shemtov/Bg_Bed/panel_shemi/src/main.cpp

// ============================================================
// PANEL SHEMI - TEST 074 - MATCHED PAIR + SEIKO NIGHT SCREENSAVER
// ============================================================
//
// Board: Waveshare ESP32-S3-Touch-LCD-7B, 1024 x 600
// TEST074 - BUILD FIX FOR AM / PM BUTTONS
//   TEST073 did not compile because seedFromRTC() calls
//   refreshAmPmButtons() before the compiler has seen its declaration.
//   Adds the forward declaration before seedFromRTC().
//   No UI behavior, RTC, RS485, massage or audio logic changed.
//   NOT YET RUN ON HARDWARE.
// TEST073 - CLOCK SETTING: DIRECT AM / PM BUTTONS
//   Removes the 12-hour ON/OFF switch from the Clock settings tab.
//   Replaces it with two small round buttons: AM and PM.
//   The selected half-day lights green; the other stays dark.
//   Pressing AM/PM changes only the half-day, not the displayed hour.
//   Hour +/- now cycles 1..12 inside the selected AM/PM half.
//   The DS3231 still stores and receives 24-hour time internally.
//   Clock display is now always 12-hour AM/PM.
//   Massage, feedback, RTC validity and RS485 logic are unchanged.
//   NOT YET RUN ON HARDWARE.
// TEST072 - BUILD FIX FOR MASSAGE SLIDER VALUE FONT
//   TEST071 did not compile because lv_font_montserrat_20 is not enabled
//   in this Waveshare LVGL build.
//   The live percentage labels above the four massage sliders now use
//   the already-enabled lv_font_montserrat_26.
//   No massage mapping, slider geometry, feedback, RTC or RS485 logic changed.
//   NOT YET RUN ON HARDWARE.
// TEST071 - MASSAGE FULL + SLIDER READOUT
//   Fixes the FULL tile mapping. FULL is UI tile index 3, not 11.
//   Tile 3 now sends CMD_ALL=100 to the BedBox.
//   UI tiles after FULL map down by one to BedBox presets 3..10.
//   FULL label changed from "מלא" to "הכל".
//   Four zone sliders are slimmer, while the knob stays visually large.
//   Each slider now shows its exact live percentage above it.
//   The displayed number follows both finger movement and BedBox feedback.
//   RTC TEST070 diagnostic remains unchanged.
//   NOT YET RUN ON HARDWARE.
// TEST070 - RTC DIAGNOSTIC MADE VISIBLE
//   TEST069 printed the RTC dump too early in boot, before the Serial
//   Monitor was reliably attached, so the useful line could be missed.
//   While CLOCK NOT READY persists, TEST070 prints the full RTC dump
//   every 5 seconds. No RTC state is changed and no Set Time is done.
//   Massage, feedback and RS485 behaviour are unchanged.
//   NOT YET RUN ON HARDWARE.
// TEST069 - RTC BACKUP / OSF DIAGNOSTIC
//   Diagnostic-only change.
//   Prints raw DS3231 time/date and status register 0x0F at boot.
//   This tells us whether the clock value survived power-off and
//   whether OSF (Oscillator Stop Flag, bit 7) is set.
//   Massage, feedback and RS485 behaviour are unchanged.
//   NOT YET RUN ON HARDWARE.
// TEST068 - MASSAGE CLOSED LOOP RESTORED
//   TEST067 restored BedBox -> panel feedback, but the current 7-inch
//   massage handlers only changed the UI and printed to USB Serial.
//   They did NOT send motor commands to the BedBox.
//   TEST068 restores the proven 4-byte BedBox downlink:
//       {bedId, cmd, target, value}
//   on the SAME onboard RS485 Serial1 bus.
//   Commands:
//       0 OFF, 1 ALL, 2 ZONE, 4 PRESET, 5 TIMER
//   The 12th "Full" tile sends ALL=100; patterns 0..10 send PRESET.
//   TEST067 feedback remains in place:
//       {bedId, 20, zone, level}
//   NOT YET RUN ON HARDWARE.
// TEST067 - BEDBOX FEEDBACK RESTORED
//   Restores the hardware-proven TEST077/BedBox TEST012 feedback behaviour
//   to the current 7-inch panel.
//   BedBox reports remain the proven 4-byte form:
//       {bedId, 20, zone, level}
//   The panel now accepts those reports on the SAME RS485 stream while
//   preserving the existing 14-byte A5 TIME/ACK traffic.
//   Slider updates are display-only: lv_slider_set_value() does not
//   generate another motor command.
//   NOT YET RUN ON HARDWARE - build/flash required for confirmation.
//
// WHAT CHANGED IN TEST 083:
//   Fixes TEST082 build failure: the generated setup Serial.println()
//   line lost its closing quote/parenthesis during text replacement.
//   TEST083 uses safe whole-line replacements and preserves valid C++.
//   Ira still uses the full 7-inch UI and receives clock/date from
//   Shemi over onboard RS485 (RX GPIO15, TX GPIO16, 115200 8N1).
//
// NOT YET COMPILED OR RUN ON HARDWARE.
//
//
// WHAT CHANGED vs TEST 055
//   THE LONG PRESS NEVER FIRED, and the approach was the fault. I
//   leaned on LV_EVENT_LONG_PRESSED, which only fires if the input
//   driver's long_press_time is what I set it to - a field inside
//   Waveshare's port that I set blind at boot and cannot verify
//   from here. Depending on it was the mistake.
//
//   THE PANEL TIMES THE HOLD ITSELF NOW. millis() on press, millis()
//   on release, subtract. Under 2 seconds flips the power; 2 seconds
//   or more opens the detail screen. No LVGL setting involved, so
//   there is nothing left to be silently wrong.
//
//   IT ACTS ON RELEASE, not at the 2 second mark. A press that
//   triggers while your finger is still down needs a timer running
//   against every tile; measuring on release is exact, needs
//   nothing running, and cannot fire twice.
//
//   AND IT PRINTS THE MEASURED HOLD - "[tile] AC held 2340 ms" - so
//   if 2 seconds turns out to be the wrong threshold for you, we
//   will be reading real numbers instead of guessing again.
//
//   PRESS_LOST is handled too: slide off the tile and nothing
//   happens, which is the standard way out of a press you did not
//   mean.
//
// WHAT CHANGED IN TEST 054 vs TEST 053
//   Alarm screen:
//     - "Hour" and "Minute" titles above their plus/minus groups,
//       the same treatment the Clock tab got in TEST 050
//     - the whole setter is CENTRED, horizontally and vertically -
//       it sat 110 px from the top before, which put it in the
//       upper third rather than the middle
//
//   THE FLEX ROW IS GONE, and it had to be: a flex row lays its
//   children out in a line and cannot put a heading over one of its
//   own columns. Absolute positions instead, exactly as the Clock
//   tab needed for the same reason.
//
//   Centred means centred on the SCREEN, so the numbers sit level
//   with the middle of the glass, not with the space left over
//   under the switches.
//
// WHAT CHANGED IN TEST 052 vs TEST 051
//   HANDS: thinner, SQUARE ended, and hollow to the tip.
//     - lv_line rounded caps turned OFF, so the ends are flat
//       rectangles instead of domes
//     - hour 20 px outer over a 12 px dark core, minute 12 over 6.
//       Was 30 over 12 and 20 over 8 - that is what made them heavy
//     - THE TRIANGLE TIPS ARE GONE. They were the weight and the
//       roundness both, and a hollow rectangle cannot end in a
//       solid point without stopping being hollow. The core now
//       runs almost to the end, so the tip reads open.
//
//   SECOND HAND IS RED, keeping the green lume dot.
//
//   NINE GETS ITS MARKER BACK - a lying pill, matching three.
//
//   THE DATE WINDOW MOVED to the right, midway between the centre
//   and the three o'clock pill, which is where the freed space is
//   now that nine is a marker again.
//
//   TEMPERATURE RIGHT, HUMIDITY LEFT was already done in TEST 050 -
//   which never ran, because it did not compile. Nothing to change;
//   it arrives with this build.
//
// WHAT CHANGED IN TEST 051 vs TEST 050
//   TEST 050 would not compile: refreshStations() was placed with
//   the radio widget pointers, above kStation and radioStation
//   which it reads. It sits just before refreshRadio now, after
//   both. Third member of the use-before-declaration family
//   tonight - so the delivery audit no longer takes a hand-made
//   list of names, it derives every file-scope variable and
//   function from the file itself and checks all of them.
//
// WHAT CHANGED IN TEST 050 vs TEST 049
//   Five prompts of remarks, all in one test.
//
//   EVERYWHERE
//     - back button is a SQUARE, 56 by 56, teal. "Square" was said
//       twice and clearly; the later garbled sentence asked for a
//       nicer colour, so amber went and teal came.
//     - the flip switch: the knob travels to the ENDS of a wider
//       pill, and when OFF the word disappears - knob position
//       says it alone. ON still says ON.
//
//   RADIO
//     - now-playing name at the top: gone
//     - title is Hebrew, drawn with font_hebrew_28
//     - station buttons are DULL until chosen; the chosen one gets
//       its full colour plus a white frame - much stronger than
//       the rest, as asked
//     - the audionode note under the stations: gone
//     - MAX at the right end of the volume slider
//
//   MASSAGE
//     - the pattern-name status at the top right (the "something I
//       do not know what sign it is"): gone. It was lblMassMode.
//     - the Massage caption beside the switch: gone
//     - the lying figure dropped well below the sliders
//
//   SETTINGS, CLOCK
//     - a title above every plus/minus group - Hour, Minute, Day,
//       Month, Year - bigger and brighter than the old grey
//     - the 12 hour switch moved to the bottom, caption under it
//
//   SETTINGS, DISPLAY
//     - "Response speed" now says what it is for: the reaction of
//       the AUTO BRIGHTNESS
//     - the switch caption sits UNDER the switch, bigger
//
//   SCREENSAVER
//     - hands rebuilt as SKELETON hands: two long bright rails with
//       a dark gap between them - an outer line with a face-dark
//       line over its middle - and a FILLED triangle tip, wider
//       than before
//     - the twelve pip is filled solid
//     - three and six are pills now, like nine was - three lying,
//       six standing, both pointing at the centre
//     - the date window moved to the LEFT, taking nine's place
//     - temperature RIGHT, humidity LEFT - swapped as asked - and
//       both drawn a step larger through transform zoom, because 48
//       is the largest font this build carries
//
// WHAT CHANGED IN TEST 049 vs TEST 048
//   TEST 048 would not compile. The new tile handlers - evACShort,
//   evFanShort - sit early in the file with the other tile code,
//   but fanSpeed, acTemp, refreshFan and refreshAC are all defined
//   hundreds of lines below them. The same use-before-declaration
//   mistake as TEST 032, caught by the compiler instead of the
//   audit because the audit only watched variables, not functions.
//
//   fanSpeed and acTemp moved up beside fanOn and acPower, where
//   they should have lived all along. refreshFan and refreshAC are
//   forward declared with the other forwards. The audit now checks
//   function calls too.
//
// WHAT CHANGED IN TEST 048 vs TEST 047
//   One line. Where the Seiko carries its red text below the
//   centre - MAGNETIC RESISTANT on the photograph - this dial says
//
//       Ira & Shemi Bengiat
//
//   in the same red, same place, small like on the watch. Spelled
//   the way Shemi spelled it. If it should be Hebrew instead, that
//   is a pre-reversed string away - say so.
//
// WHAT CHANGED IN TEST 047 vs TEST 046
//   The watch face redone against the photograph Shemi sent - a
//   Seiko Prospex Tuna. What was taken from it:
//
//   HANDS. The hour hand is BROAD - a wide shaft with a pointed
//   tip. The minute hand is longer and slimmer, same pointed tip.
//   The second hand is a thin line with a LUME DOT near the tip and
//   a counterweight tail past the centre - that dot is the most
//   recognisable thing on the watch and it moves with the hand,
//   realigned every second.
//
//   A DATE WINDOW AT THREE, where the Tuna has its date: a small
//   framed rectangle showing the day of the month, updated when the
//   day changes. The dot at three gave its place to it.
//
//   A HORIZONTAL PILL AT NINE, as on the photograph, instead of a
//   round dot.
//
//   The pips at twelve and six stay as Shemi specified them - the
//   six o'clock pip is his instruction and it stands even though
//   the Tuna itself carries a dot there.
//
//   Dots remain at 1, 2, 4, 5, 7, 8, 10, 11.
//
// WHAT CHANGED IN TEST 046 vs TEST 045
//   TWO FACTS BEFORE THE FEATURES, checked in the repo rather than
//   assumed:
//     - The AC detail screen here was a stub. The old panel's full
//       one - modes, fan speeds, swing, the honest "shows what was
//       last commanded" note - is now ported: Cool/Heat/Dry/Fan/
//       Auto, Low/Med/High/Auto, Swing on/off, temp 16-30, room
//       reading beside the target.
//     - There is NO fan screen in the old panel to copy. buildFan
//       does not exist in that file; the fan screen here was
//       written fresh for this board in TEST 017. It stays as it
//       is. If TEST 082 had one, it never reached the repo.
//
//   SHORT PRESS AND LONG PRESS ON THE HOME TILES, for fan and AC:
//     - a short press flips the power and stays on the home screen
//     - holding for 2 seconds opens the detail screen
//   The touch driver's long press threshold is set to 2000 ms at
//   boot - the LVGL default is 400, which is a twitch, not a hold.
//   Massage and radio tiles keep their single press - Shemi asked
//   for the two devices you mostly just switch on and off.
//
//   The AC power on the tile and the one on the screen go through
//   ONE function, so the two can never disagree about what "on"
//   means.
//
// WHAT CHANGED IN TEST 045 vs TEST 044
//   Watch face again, per Shemi:
//     - the dots doubled: 40 px core, about 6 mm, glow scaled with
//       them
//     - the arrowheads cut down - they were slabs; a dive watch
//       hand is mostly shaft with a modest tip
//     - a second pip at SIX, mirrored: flat edge at the bottom,
//       apex pointing up at the centre. The dot at six gave its
//       place to it, the same way twelve's did.
//     - temperature TOP LEFT, humidity TOP RIGHT, both in the same
//       green as the face, both whole numbers - no decimal
//     - the temperature was already in the largest font this build
//       carries (48). Dropping the decimal makes the digits the
//       whole string, which reads larger without a new font.
//
//   A photograph of the watch to imitate is on its way from Shemi;
//   this pass covers what was already specified in words.
//
// WHAT CHANGED IN TEST 044 vs TEST 043
//   Massage screen, reworked to what you asked:
//
//   THE TWELVE COLOURS ARE GONE. Tiles are back to the quiet dark
//   grey, and the chosen one lights green - the TEST 081 behaviour.
//   kPatCol was deleted outright, not left as dead weight.
//
//   THE TITLE IS HEBREW NOW - the word everyone actually says,
//   with a geresh, stored pre-reversed like every Hebrew string
//   here. It is drawn with font_hebrew_28, which also makes it a
//   little larger than the 26 point Latin titles. 28 is the only
//   Hebrew size compiled into this build; noticeably bigger than
//   that means generating a new font, which is a separate job -
//   say so if you want it.
//
//   THE ZONE NAMES UNDER THE SLIDERS ARE GONE. In their place a
//   small figure lies under the four sliders, head at the left
//   under the first, feet at the right under the fourth - so the
//   mapping is drawn instead of written. Head, torso, legs, from
//   LVGL primitives, nothing clickable.
//
//   THE RED KIBUI BUTTON IS GONE. One flip switch, the same one the
//   radio has, and nothing else. Its handler went with it.
//
//   THE TIMER SLIDER ENDS AT THE 60 BUTTON, same rule as the radio:
//   buttons at 20, 162 and 304, each 130 wide, row ends at 434, so
//   the slider is 414 wide from 20.
//
//   THE "press the running one again" HINTS ARE GONE, from both
//   screens. The behaviour stays; the label explaining it does not.
//
// WHAT CHANGED IN TEST 043 vs TEST 042
//   THE TOGGLE IS A FLIP SWITCH NOW. The ON/OFF button told you the
//   state in words; this one shows it in position, like the switch
//   on a wall. A pill shaped track with a round knob: knob LEFT and
//   grey track when off, knob RIGHT and green track when on, the
//   word sitting on the empty side. Still a tap and only a tap -
//   the knob does not drag, pressing anywhere flips it.
//
//   All six toggles get this - radio, massage, alarm armed, every
//   day, 12 hour, auto brightness - because two different switch
//   styles on one panel is one too many. The handlers, again,
//   unchanged: same LV_STATE_CHECKED underneath.
//
//   RADIO SCREEN LAYOUT, as asked:
//     - the sleep slider now ends exactly where the 60 minute
//       button ends. Buttons sit at 24, 164 and 304, each 128 wide,
//       so the row ends at 432 - the slider is 408 wide from 24.
//     - the radio flip switch moved to the right side of the
//       screen, clear of the timer row.
//
//   AND ONE RULE INTO THE PROJECT KNOWLEDGE, not this file: when
//   the radio starts, audionode fades the volume from silence up to
//   the set level over about 1.5 seconds. Never straight in at full
//   set volume. The panel only sends the play command; the ramp
//   belongs to the node that owns the DAC. Recorded so it is built
//   that way when audionode grows its bus interface.
//
// WHAT CHANGED IN TEST 042 vs TEST 041
//   TEST 041 would not compile. buildSettings() had two locals both
//   called sb - the "Set time and date" button in the Clock tab, and
//   the "Screensaver brightness" caption I added to the Display tab
//   in TEST 039. Both tabs are built inside the SAME function, so
//   they share one scope. The second one is sbCap now.
//
//   I checked every other builder the same way afterwards. The two
//   apparent duplicates in buildMassage and buildRadio are each a
//   local b inside a separate for loop, which are separate scopes -
//   those are fine.
//
// WHAT CHANGED IN TEST 041 vs TEST 040
//   Massage screen:
//     - a timer slider, 5 to 60 minutes, beside the three buttons,
//       working the same way the radio one does
//     - a large ON / OFF toggle on the right
//     - a different colour for each of the twelve patterns
//     - the numbers above the zone sliders removed
//     - Hebrew zone names under them instead of 1 2 3 4
//   And the back arrow is amber now, on every screen.
//
//   THE PATTERN COLOURS ARE NOT FROM TEST 081, and I checked before
//   choosing. That version built all twelve tiles with no bg_color
//   at all and only lit the selected one, so there was nothing to
//   copy. These twelve are mine, spread around the wheel so no two
//   neighbours in the grid are close.
//
//   THE ZONE NAMES ARE FROM TEST 075 and are stored back to front,
//   like every other Hebrew string here - LVGL has no bidirectional
//   text. Do not reorder them in an editor.
//
//   THE MASSAGE TIMER ACTUALLY RUNS NOW. It was a number that got
//   printed and nothing else. It counts down, shows the minutes
//   left, and switches the massage off at zero - rollover safe, the
//   same way the radio timer is.
//
//   IT IS NOT STORED. The EEPROM record is a full 16 byte page and
//   the next byte would push it over into a second page, which the
//   AT24C32 does not write through - it wraps. Not worth restructing
//   the record for a value you set per session anyway.
//
// WHAT CHANGED IN TEST 040 vs TEST 039
//   EVERY lv_switch IS GONE. There were five - auto brightness, 12
//   hour, alarm armed, alarm repeat - and they are small, the state
//   is hard to read across a room, and they invite a drag.
//
//   Replaced by a large button that carries its own state: 150 by
//   56, green and reading ON when set, dark grey and reading OFF
//   when not. LV_OBJ_FLAG_CHECKABLE makes a press toggle it, so it
//   is a tap and only a tap - there is nothing to slide.
//
//   The handlers did not have to change. They already read
//   LV_STATE_CHECKED, and a checkable button carries exactly the
//   same state a switch did.
//
//   RADIO SCREEN: the Stop button at the top right is gone, and the
//   sleep row's Off button is now a RADIO ON / OFF toggle in its
//   place. Switching the radio off also cancels the sleep timer -
//   there is nothing left for it to switch off.
//
//   Turning it on with no station chosen selects the first one,
//   because a power switch that appears to do nothing is worse than
//   one that makes an obvious choice.
//
//   TO CANCEL THE TIMER WITHOUT STOPPING THE RADIO, press the
//   active preset again. It is written on the screen, because a
//   hidden gesture is not a feature.
//
//   THE SLEEP SLIDER NOW STOPS AT 60 MINUTES, matching the three
//   buttons. It ran to 120 before, which put most of its travel
//   past anything the buttons offered.
//
// WHAT CHANGED IN TEST 039 vs TEST 038
//   TWO SLIDERS ON THE DISPLAY TAB, and a correction first: in TEST
//   081 the screensaver DELAY was a dropdown, ddSaver, with four
//   options. The slider there, range 1 to 60, was "Night backlight
//   (screensaver)" - the screensaver's brightness. So you were
//   remembering a real slider, but it controlled the other thing.
//
//   Both are sliders now:
//     - delay: Never, 15 s, 30 s, 1, 2, 5, 10, 20, 30 minutes
//     - brightness: 1 to 60 percent, replacing the hard coded 8
//
//   THE BRIGHTNESS ONE WAS A GENUINE GAP. SAV_BRIGHT was a constant
//   in the source, so the one number that decides how much light
//   sits next to a sleeping head could only be changed by
//   rebuilding.
//
//   NOTHING STORED IS LOST, and that took some care. Byte 12 held a
//   delay index into a five entry table; the new table has nine, so
//   the same number now means something different. Rather than bump
//   the record version and wipe every setting you have tuned, the
//   new delay goes in byte 14 as index PLUS ONE - so zero means
//   "never written", and an older record falls back to byte 12 and
//   is translated. The brightness rides in the high nibble of byte
//   12, which was always zero before and reads as "use the default".
//
//   The slider moves in nine steps rather than freely. A screensaver
//   delay of 7 minutes 23 seconds is not a thing anyone wants, and
//   a free slider makes hitting exactly 5 minutes a fiddle.
//
// WHAT CHANGED IN TEST 038 vs TEST 037
//   THE MISSING TEMPERATURE WAS NOT THE SENSOR. lv_conf.h has
//   LV_SPRINTF_USE_FLOAT 0, so LVGL's own printf DISCARDS %f
//   silently - which is why the screen showed a degree sign and a
//   percent sign with nothing in front of them.
//
//   It was wrong in four places, not one: the screensaver
//   temperature and humidity, the lux reading in Settings, and the
//   room temperature on the AC screen. All four now format with the
//   C library snprintf and hand LVGL a finished string. Every one
//   of them had been printing an empty number since the day it was
//   written.
//
//   NUMERALS REPLACED BY DOTS. Twenty pixels across, which on a 7
//   inch 1024 wide panel is about 3 mm - the screen is roughly 154
//   mm wide, so 6.65 pixels per mm. Glowing, in three concentric
//   circles: wide and faint, medium, then the bright core.
//
//   The separate ring of small tick marks is gone with them. Two
//   rings of markers was one too many once the numerals left.
//
//   THE PIP AT TWELVE IS INVERTED - flat edge at the top, point
//   downwards, as asked - and the dot at twelve is dropped so the
//   pip stands alone there, which is what a dive bezel does.
//
//   THE ARROWHEADS ARE TRIANGLES NOW, not a thick stub of line.
//   Three points, closed, drawn with a wide stroke: LVGL cannot
//   fill a polygon, but at this size the strokes meet in the middle
//   and it reads as solid. The corners are recomputed as the hands
//   turn, so the triangle always points along the hand.
//
// WHAT CHANGED IN TEST 037 vs TEST 036
//   THE STATION LIST IS THE REAL ONE, recovered from TEST 069 in
//   the repo rather than invented: Kan 88, Kan Gimel, Galgalatz,
//   Eco 99, Reshet Bet, Kol HaMusica, Groove Salad, Drone Zone.
//   The colours are the ones already chosen there - Kan's own brand
//   colours for the first two - so every button is a different
//   colour, as asked. My eight placeholders are gone.
//
//   The old note said Kan 88 and Kan Gimel carry real stream URLs,
//   pulled from the data-player-hls-src attribute on kan.org.il.
//   Those URLs are NOT in this panel and this panel plays nothing;
//   they belong on audionode when the bus exists.
//
//   THE LABELS ARE 26 POINT, up from 16, which is the largest this
//   lv_conf.h builds for Latin text.
//
//   HEBREW: NOT DONE, AND THIS IS THE REASON. There is no
//   bidirectional engine, so Hebrew has to be stored back to front
//   by hand. "Kan 88" and "Eco 99" mix Hebrew with digits, and the
//   digits must NOT be reversed while the letters must - a rule I
//   would be applying blind, with no way to check it here. Say the
//   word and I will write them out, but I am not guessing at the
//   spelling of your own radio stations.
//
//   A RUNNING SLEEP TIMER IS NOW VISIBLE FROM ACROSS THE ROOM: a
//   green badge with the minutes left, blinking once a second, on
//   the radio screen AND on the radio tile of the home screen. The
//   question "am I on a timer" gets answered without opening
//   anything.
//
//   IT BLINKS BY TOGGLING OPACITY, not by rebuilding. On an RGB
//   panel anything that redraws a large area every second shows as
//   a twitch; a 60 pixel badge changing opacity does not.
//
// WHAT CHANGED IN TEST 036 vs TEST 035
//   The screensaver reworked to what you asked for:
//     - hour numerals glowing green
//     - a dive watch pip at twelve
//     - broad bright arrowheads on the hour and minute hands
//     - temperature large on the right, one decimal
//     - humidity on the left, whole percent
//     - the digital time at the bottom removed
//     - a small red alarm clock at bottom right when one is armed
//
//   MONTSERRAT 48 ENABLED in lib/lv_conf.h. 26 was the largest
//   built, and 26 is not "much bigger". Second line touched in that
//   vendor file, after LV_MEM_SIZE.
//
//   LVGL HAS NO GLOW, so it is faked: a dark green copy of each
//   numeral offset two pixels in four directions, with the bright
//   one on top. On a dark face that reads as a halo. It costs five
//   labels per numeral, sixty in total, which is why the 128 KB
//   heap mattered.
//
//   THE ARROWHEADS ARE SEPARATE LINES, not wider hands. A hand
//   drawn at double width for its whole length is a slab; a short
//   double width segment at the tip reads as an arrow. Two objects
//   per hand instead of one.
//
//   TEMPERATURE IS CLAMPED TO ONE DECIMAL AND TO A SANE RANGE. The
//   SHT3x is checksummed, but a checksum only proves the bytes
//   arrived intact - so anything outside -10..60 draws as "--"
//   rather than as a confident wrong number beside a sleeping head.
//
//   THE ALARM CLOCK IS THE SAME 160x160 PHOTOGRAPH, drawn at 37
//   percent with lv_img_set_zoom. No second asset, no extra flash.
//
// WHAT CHANGED IN TEST 035 vs TEST 034
//   A proper sleep timer on the radio screen: 10, 30 and 60 minute
//   buttons, a slider for anything else up to two hours, an Off
//   button, and the time remaining counting down in minutes.
//   The old fixed "Sleep 30" button is gone.
//
//   THE COUNTDOWN IS ROLLOVER SAFE. millis() wraps after about 49
//   days, and a panel meant to sit on a headboard for years WILL
//   cross that. Comparing millis() >= end fails exactly once when
//   it wraps - the radio would stop dead in the middle of a night,
//   months from now, for no visible reason. Subtracting first and
//   testing the sign is correct across the wrap.
//
//   SETTING IT WHILE THE RADIO IS OFF DOES NOTHING. There is
//   nothing to stop, and a timer counting down against silence only
//   creates a surprise later.
//
//   STOPPING THE RADIO CANCELS THE TIMER, so it cannot fire against
//   a station you started afterwards and expected to keep playing.
//
//   THE CHOSEN LENGTH IS REMEMBERED in byte 13 of the EEPROM record,
//   which was padding. An older record reads 0 and is corrected to
//   30 minutes on load. No version bump.
//
//   AND IT STILL COMMANDS NOTHING. audionode holds the audio and the
//   bus to reach it does not exist. The timer runs, the state
//   changes, the screen says so. That is the honest extent of it.
//
// WHAT CHANGED IN TEST 034 vs TEST 033
//   A second switch on the alarm screen: every day, or once.
//
//   ONCE DISARMS WHEN IT STARTS RINGING, not when you stop it. That
//   way it cannot fire again tomorrow no matter what you do with it
//   this morning - stop it, snooze it, ignore it until it gives up,
//   or walk out of the room.
//
//   SNOOZE STILL WORKS AFTER IT DISARMS. Snooze runs off its own
//   target rather than the armed flag, so a once-only alarm can
//   still be pushed nine minutes and will still come back this
//   morning. It just will not be there tomorrow.
//
//   STORED AS "ONCE", NOT AS "REPEAT". Bit 3 of the flags byte was
//   always zero in existing records, and every alarm until now
//   repeated daily. Storing the flag the other way round would make
//   every saved alarm silently become once-only on the first boot
//   after flashing. So 0 means every day, which is what those
//   records meant. No version bump, nothing lost.
//
// WHAT CHANGED IN TEST 033 vs TEST 032
//   TEST 032 would not compile. lastTouchMs was declared inside the
//   screensaver block, which sits near the end of the file, while
//   evAnyPress and evSaverAfter both use it hundreds of lines
//   earlier. When I hoisted saverAfterMs and kSaverOpts above the
//   EEPROM code I moved two of the five and left three behind.
//   saverOn and blBeforeSaver had the same problem waiting one
//   error further on. All five now sit together.
//
// WHAT CHANGED IN TEST 032 vs TEST 031
//   The boot photograph is back. include/boot_photo.h has been
//   sitting in the repo unused since the port - two 800x480
//   baseline JPEGs, yours and Ira's, with PANEL_ID choosing.
//
//   THE OLD DRAW ROUTE DOES NOT EXIST HERE. TEST 081 handed each
//   decoded block straight to gfx->draw16bitRGBBitmap from
//   Arduino_GFX, and this board does not use that library at all -
//   it is esp_lcd plus LVGL. Same decoder, different destination:
//   JPEGDEC writes into a PSRAM buffer, and that buffer is shown as
//   an ordinary LVGL image.
//
//   IT DECODES INTO PSRAM, NOT INTO LVGL'S POOL. 800x480 at two
//   bytes is 768,000 - six times the whole LVGL heap. PSRAM has 8 MB
//   and the buffer is handed back the moment the photo leaves the
//   screen, so nothing stays resident.
//
//   THE JPEG IS COPIED OUT OF FLASH FIRST. JPEGDEC needs a writable
//   pointer and PROGMEM is not one. Same reason TEST 081 did it.
//
//   RGB565_LITTLE_ENDIAN, to match LV_COLOR_16_SWAP 0. Getting this
//   wrong gives a recognisable photograph in wrong colours.
//
//   IF ANYTHING FAILS IT JUST GOES TO THE HOME SCREEN. No allocation
//   for the buffer, no decoder, a corrupt file - the panel says so
//   on serial and carries on. A boot screen is not worth a boot
//   loop.
//
//   PANEL_ID 1 HERE. Setting it to 2 builds Ira's panel from this
//   same file and shows her photograph instead, which is how you
//   can tell at a glance which board you just flashed.
//
// WHAT CHANGED IN TEST 031 vs TEST 030
//   THE DRAWN CLOCK IS GONE. The tile carries your photograph now -
//   the red one when armed, the black one when off. Cut from the
//   picture you sent, 160x160, in include/alarm_img.h.
//
//   NO ALPHA CHANNEL. The background is baked to TILE_BG_OFF
//   instead. Alpha costs 50 percent more flash and a blend on every
//   redraw, and these two images only ever sit on that one tile
//   colour. If the tile colour ever changes, the images have to be
//   regenerated - that is the price, and it is the right trade
//   here.
//
//   RGB565 LITTLE ENDIAN, LV_IMG_CF_TRUE_COLOR - matched to
//   tile_img.h rather than assumed. lv_conf.h has LV_COLOR_DEPTH 16
//   and LV_COLOR_16_SWAP 0; getting the byte order wrong gives a
//   recognisable picture in wrong colours, which is a confusing
//   failure to chase.
//
//   THE SCREENSAVER IS BACK, ported from buildAnalog() in TEST 081
//   and rescaled from 800x480 to 1024x600: round face, twelve
//   ticks, the numbers 1 to 12, hour, minute and second hands, and
//   below them the time in figures with temperature and humidity.
//
//   THE SECOND HAND MOVES ONCE A SECOND, THE REST ONLY WHEN THEY
//   CHANGE. Redrawing all three every second on an RGB panel is
//   what made the old screen twitch.
//
//   IT DIMS. The screensaver has its own brightness, well under the
//   normal one, because it is the thing that sits lit next to a
//   sleeping head. Touch anywhere returns to the home screen and
//   restores the brightness.
//
//   THE IDLE DELAY IS A SETTING, in the Display tab, with Never as
//   an option so it can be switched off.
//
// WHAT CHANGED IN TEST 030 vs TEST 029
//   The alarm clock was drawn and you could not see it. Most likely
//   because I chose 0x1A1A1A for the OFF body against a tile
//   background of almost the same darkness - black on black.
//
//   OFF IS NOW GREY, NOT BLACK. 0x565A66 against the tile, with a
//   lighter rim around the body and the bells. Armed is still red.
//   The two states are unmistakable and BOTH are visible.
//
//   THE SET TIME IS PRINTED ON THE TILE, under the clock, so the
//   home screen answers "when is it set for" without opening
//   anything - and so the tile is obviously not empty.
//
//   THE BELLS SHAKE WHILE IT RINGS. Four pixels left and right, in
//   step with the motor pulse. This is the thing a drawn icon can
//   do that a photograph cannot, and it was the argument for
//   drawing it.
//
//   AND IT SAYS SO ON SERIAL: "[alarm] icon built" at boot, with
//   the state. If that line does not appear, the icon is not being
//   constructed and the problem is somewhere else entirely - no
//   more guessing from here about whether it exists.
//
// WHAT CHANGED IN TEST 029 vs TEST 028
//   Still said Thursday on a Friday. The arithmetic was already
//   right - Zeller returns h=6 for 4 September 2026 and the mapping
//   gives kDow[6], "Fri". The wrong day was not being calculated.
//   IT WAS BEING READ.
//
//   now.dow came from DS3231 register 0x03, and that register is
//   only ever written when the clock is set. The 5 that was put
//   there before the TEST 017 fix has been sitting in the chip ever
//   since, and every boot faithfully read it back.
//
//   THE REGISTER IS NO LONGER THE SOURCE OF TRUTH. Day of week is
//   derived entirely from the date, so there is no reason to trust
//   a byte that can be stale, wrong, or set by some other device
//   sharing the chip. It is computed on every read now.
//
//   This kills the whole family of failures rather than the one
//   instance, and it corrects the display without you setting the
//   clock again.
//
//   The register is still WRITTEN when the clock is set, so anything
//   else that ever reads this chip sees a sensible value.
//
// WHAT CHANGED IN TEST 028 vs TEST 027
//   TEST 027 runs. A 12 hour option added, as a switch in the Clock
//   tab, stored with everything else.
//
//   THE CHIP STAYS ON 24 HOUR NO MATTER WHAT THE SCREEN SHOWS. The
//   DS3231 hour register carries a 12/24 mode bit, and writing 12
//   hour values into it means converting in both directions around
//   midnight and noon - the two times that break every naive
//   conversion. One representation in the hardware, converted only
//   where it is drawn.
//
//   IT REUSES A SPARE BIT rather than bumping the EEPROM version.
//   Bit 2 of the flags byte was previously always zero, so an
//   existing record reads as 24 hour, which is what it was. No
//   version change, no settings lost.
//
//   MIDNIGHT IS 12 AM AND NOON IS 12 PM. Written out because the
//   obvious formula, h % 12, turns both into 0 and prints "0:15 AM".
//
// WHAT CHANGED IN TEST 027 vs TEST 026
//   THE BOOT LOOP IS SOLVED, and the decoded backtrace named it:
//       lv_obj_add_style   lv_obj_style.c:96
//       lv_btn_create      lv_btn.c:53
//       setBtn             main.cpp:1830
//       navBack            main.cpp:1954
//
//   Line 96 is  obj->styles[j] = obj->styles[j - 1];  - a write
//   through the pointer that lv_mem_realloc had just returned on
//   the line above. The register dump closes it: EXCVADDR was 0x38,
//   which is index 7 times the 8 byte style record. styles was
//   NULL. THE REALLOC FAILED. LVGL had run out of memory.
//
//   48 KB was not enough for seven screens. buildHome and
//   buildSettings fit; it died part way into the fourth.
//
//   TWO CHANGES, AND BOTH ARE NEEDED.
//
//   1. LV_MEM_SIZE 48K -> 128K in lib/lv_conf.h. That file belongs
//      to Waveshare and this is the one line touched in it. It has
//      to be there: LV_MEM_SIZE is defined outright, so a -D in
//      build_flags loses to the header.
//
//   2. SCREENS ARE BUILT ON DEMAND. Building all seven at boot to
//      show one was wasteful even when it fit. Each is built the
//      first time it is opened and kept afterwards, so the panel
//      only pays for what has been used.
//
//   AND IT REPORTS ITS OWN MEMORY NOW. lv_mem_monitor after every
//   screen build, plus an m command on serial. Guessing at how much
//   room is left is what put us here.
//
// WHAT CHANGED IN TEST 026 vs TEST 025
//   Step prints during setup, kept - they cost nothing and they
//   name the failing stage instantly.
//
// WHAT CHANGED IN TEST 025 vs TEST 024
//   TEST 025 got the panic message:
//       Guru Meditation Error: Core 1 panic'ed (LoadProhibited)
//       EXCVADDR: 0x00000038
//   after "[cfg] empty - using defaults".
//
//   LoadProhibited with EXCVADDR 0x38 is a READ THROUGH A NULL
//   POINTER - something was NULL and a field 56 bytes into it was
//   read. Not memory exhaustion, which would assert in lv_mem, and
//   not the EEPROM, which had already printed its result.
//
//   Everything up to that point succeeded: panel ok, all four
//   device handles ok, the EEPROM read and reported itself empty.
//   The crash is in the seven build functions that run next, and
//   none of them gets far enough to print.
//
//   THIS VERSION ONLY PRINTS. A line before and after each build
//   step, so the next boot names the function instead of me
//   guessing which of seven it is. No behaviour changes.
//
// WHAT CHANGED IN TEST 025 vs TEST 024
//   Nothing in this file - only the exception decoder in
//   platformio.ini.
//
// WHAT CHANGED IN TEST 024 vs TEST 023
//   NOTHING IN THIS FILE. The only change in TEST 025 is one line
//   in platformio.ini - the exception decoder - so that the boot
//   loop prints line numbers instead of raw addresses.
//
//   The board compiles and then reboots in a loop. I am not
//   rewriting anything until the panic message says where it dies.
//   The two candidates I would otherwise be guessing between are
//   the EEPROM read at boot (new in TEST 022) and LVGL running out
//   of heap now that seven screens are built and kept alive at once
//   (LV_MEM_SIZE is 48 KB). Guessing between them by rewriting is
//   exactly how the last two rounds went wrong.
//
// WHAT CHANGED IN TEST 024 vs TEST 023
//   TEST 022 and 023 would not compile. One line, mine.
//
//   eeWaitReady() passed `handle` to i2c_master_probe. `handle` is
//   a DEV_I2C_Port, which is a STRUCT - the bus pointer is the .bus
//   member inside it. probeAddr() three hundred lines up gets this
//   right and has done since TEST 010; I wrote the new function
//   from memory instead of copying the one already working in the
//   same file. Known-good beats deduced, and I did not follow it.
//
//   Also cleaned: three warnings about LV_PART_ITEMS |
//   LV_STATE_CHECKED. LVGL declares the two as separate anonymous
//   enums and this toolchain deprecates a bitwise operation between
//   them, so both are cast to lv_style_selector_t first, which is
//   the type the function wants anyway. Warnings only - they were
//   never what stopped the build.
//
// WHAT CHANGED IN TEST 023 vs TEST 022
//   The alarm tile is a drawn alarm clock now - two bells, a round
//   body, a white face, hands and feet. RED WHEN ARMED, BLACK WHEN
//   OFF, exactly as asked.
//
//   IT IS DRAWN, NOT AN IMAGE, and that turns out to be the better
//   answer anyway. tile_img.h alone is nearly 4 MB; this costs a
//   few dozen bytes. It recolours between red and black by changing
//   two style properties instead of carrying two bitmaps. It scales
//   to any size without re-exporting. And when the ring animation
//   goes in later, the bells can shake - a photograph cannot.
//
//   THE PARTS ARE NOT CLICKABLE. lv_obj_create makes a clickable
//   object by default, so nine shapes stacked on the tile would
//   swallow every touch and the tile would stop responding. Each
//   part has CLICKABLE cleared, which makes it invisible to hit
//   testing and lets the press land on the tile underneath.
//
//   THE HANDS POINT AT THE ALARM TIME. Not decoration - the tile
//   shows when it is set for, so the home screen answers the
//   question without opening anything. Redrawn only when the time
//   changes, never on a timer.
//
// WHAT CHANGED IN TEST 022 vs TEST 021
//   Every tuned value is now kept in the AT24C32 at 0x57 - the 4 KB
//   EEPROM on the RTC module, found in the very first scan and
//   unused until now. Stored: auto brightness on/off, darkest,
//   brightest, response speed, haptic strength, haptic length,
//   alarm time and whether the alarm is armed.
//
//   IT IS NOT FLASH AND IT DOES NOT CARE ABOUT REFLASHING. Loading
//   new firmware wipes the ESP32, not the chip on the clock module.
//   The settings survive a rebuild, which is exactly why this is
//   the right place for them.
//
//   WRITES ARE DELAYED THREE SECONDS, AND THAT IS THE WHOLE POINT.
//   A slider sends VALUE_CHANGED dozens of times while a finger
//   moves. Writing on each one would be dozens of write cycles for
//   one adjustment. The change marks the settings dirty; three
//   quiet seconds later it is written once. An AT24C32 is good for
//   about a million cycles, and this keeps a lifetime of adjusting
//   nowhere near it.
//
//   IT WAITS FOR THE WRITE CYCLE BY POLLING, NOT BY GUESSING. The
//   chip stops answering for roughly 5 ms after a write while it
//   burns the page, so the code probes it until it acknowledges,
//   with a ceiling in case it never does. A blind delay is either
//   too short and corrupts, or too long and stalls the UI.
//
//   MAGIC, VERSION AND CHECKSUM. A blank EEPROM is all 0xFF, and a
//   layout change makes yesterday's bytes mean something else.
//   Either one loads as garbage - a backlight of 255, an alarm at
//   minute 65535. Anything that does not match falls back to the
//   built-in defaults and says so on serial.
//
//   SIXTEEN BYTES AT ADDRESS 0, one page. The AT24C32 writes 32
//   bytes at a time and a write that crosses a page boundary wraps
//   to the start of the page instead of continuing - a classic way
//   to corrupt the front of a record. Staying inside one page
//   avoids the question entirely.
//
//   THE ADDRESS IS TWO BYTES, high then low. The AT24C02 on some
//   other RTC modules takes one. Sending one byte to this chip
//   writes to the wrong place and reads back nonsense.
//
// WHAT CHANGED IN TEST 021 vs TEST 020
//   The automatic brightness now reacts quickly, and how quickly is
//   a slider rather than a number I picked.
//
//   TEST 019 WAS TOO SLOW AND THE ARITHMETIC SAYS SO. It ran once a
//   second and moved one point per run, so 12 percent to 100 was 88
//   seconds. Turning on a lamp and waiting a minute and a half is
//   not a screen following the room.
//
//   IT RUNS EVERY 100 ms NOW, on its own timer, and the lux is read
//   there too. Ten reads a second of two bytes each is nothing on a
//   400 kHz bus.
//
//   THE SENSOR IS THE FLOOR, NOT THE CODE. The BH1750 in high
//   resolution finishes a conversion about every 120 ms, so nothing
//   can respond faster than that no matter where the slider sits.
//   Low resolution mode would be 16 ms but quantises to 4 lx, which
//   is useless at the 1 to 50 lx end where a bedroom actually
//   lives. High resolution stays.
//
//   ONE SLIDER, 1 TO 10, moves both halves together: the averaging
//   constant and how far the backlight may travel per tick. At 1 it
//   is the slow smooth behaviour of TEST 019. At 10 the full range
//   crosses in about a second, which is as close to instant as the
//   sensor allows.
//
//   THE FEEDBACK RISK GROWS WITH SPEED, and this is the part worth
//   reading twice. If the BH1750 can see the screen, brighter means
//   higher reading means brighter. TEST 019 was slow enough that
//   the loop could barely sustain itself. A fast loop oscillates
//   readily. IF THE BRIGHTNESS PUMPS UP AND DOWN ON ITS OWN, turn
//   the speed down first to confirm that is what it is, then move
//   the sensor. The code cannot fix a sensor that sees its own
//   output.
//
// WHAT CHANGED IN TEST 020 vs TEST 019
//   An alarm, on the spare tile. It rings by pulsing the panel
//   motor, as asked. Audio through audionode goes in when the bus
//   exists.
//
//   THE RED ALARM ICON IS NOT IN THE REPO, so the tile carried
//   LV_SYMBOL_BELL. Replaced in TEST 023 by a drawn clock.
//
//   TWO THINGS YOU DID NOT ANSWER, so I chose and I am saying so
//   rather than burying it: ONE alarm, and it repeats EVERY DAY.
//   Weekday selection and a second alarm for Ira are both small
//   additions on top of this, not rewrites.
//
//   IT WILL NOT RING ON AN UNSET CLOCK. If the oscillator stop flag
//   is up the time registers still return a number and it is
//   meaningless, so an alarm armed against it would go off at a
//   random moment. The check is the same one the display uses.
//
//   IT FIRES ON THE MINUTE CHANGING, not on the minute matching.
//   Matching would re-trigger every second for sixty seconds. The
//   very first tick after boot only records the minute and never
//   fires, so powering up inside the alarm minute does not set it
//   off.
//
//   EVERYTHING IS MINUTE OF DAY, so snooze crosses midnight without
//   a special case. 23:55 plus nine minutes is 00:04, and the
//   arithmetic does that on its own.
//
//   THE RING PULSE IGNORES THE TOUCH SETTINGS. Feedback tuned down
//   to 20 percent for a pleasant tap would make a useless alarm, so
//   the ring uses its own strength and length.
//
//   IT GIVES UP AFTER TWENTY MINUTES. An alarm nobody is there to
//   stop should stop by itself rather than buzz at an empty room
//   until the power goes.
//
//   HONEST LIMIT: a motor on the headboard is a weak alarm, and you
//   have already said the tick is barely noticeable. This will not
//   reliably wake you. The mattress motors over RS-485 are the real
//   answer, and they also give each side its own silent alarm.
//
// WHAT CHANGED IN TEST 019 vs TEST 018
//   The BH1750 now drives the backlight. Brighter room, brighter
//   screen. Two sliders set the ends of the range and a switch
//   turns the whole thing off.
//
//   THE MAPPING IS LOGARITHMIC, NOT LINEAR, and this is the
//   difference between working and useless. The eye responds to
//   light roughly logarithmically, and lux does not: a lit bedroom
//   is around 50 lx, an office 400, a window on a grey day 2000.
//   Mapped linearly to 0-100, everything from dusk to indoors sits
//   in the bottom few percent and the screen is dim all evening,
//   then pinned at maximum the moment a lamp comes on. log10 of the
//   lux is mapped instead, from 1 lx to 1000 lx.
//
//   IT IS SMOOTHED AND IT MOVES SLOWLY. Your own logs had lux
//   swinging 31 to 222 inside one minute - someone walking past,
//   a shadow, a cloud. Driving the backlight from that directly
//   makes the screen breathe. So the lux runs through an
//   exponential average, and the backlight then walks toward its
//   target one point per second. A cloud is invisible; walking into
//   the room takes a few seconds to answer, which is what a person
//   expects anyway.
//
//   THERE IS A DEADBAND. Without one the backlight hunts by a point
//   forever, and on this panel a backlight step is visible.
//
//   THE FEEDBACK LOOP IS THE REAL HAZARD, and it depends on where
//   you mounted the sensor. If the BH1750 can see the screen or its
//   reflection, brighter screen means higher reading means brighter
//   screen. The slow time constant and the deadband make that
//   oscillation hard to sustain, but they do not remove it. IF THE
//   BRIGHTNESS EVER PUMPS SLOWLY UP AND DOWN ON ITS OWN, that is
//   this loop, and the fix is the sensor's position, not the code.
//
//   TWO SLIDERS, ONE SWITCH, NO THIRD SLIDER. With Auto on, Min and
//   Max are the ends of the range the room maps onto. With Auto
//   off, Max IS the fixed manual brightness and Min is ignored. So
//   the manual control from TEST 016 has not been lost - it is the
//   same slider wearing its other hat.
//
// WHAT CHANGED IN TEST 018 vs TEST 017
//   A third settings tab, Touch, with two sliders: pulse strength
//   and pulse length. Same two numbers the v and h serial commands
//   set, now under a finger.
//
//   THE TEST PULSE FIRES ON RELEASE, NOT ON VALUE CHANGE. A slider
//   sends VALUE_CHANGED dozens of times while the finger moves, and
//   firing on each one would buzz continuously through the drag.
//   The number updates live; only the vibration waits for the
//   finger to lift, so what you feel is the value you chose.
//
//   Length runs 20 to 500 ms. Below about 40 ms an ERM has not
//   spun up and there is nothing to feel - that is the whole reason
//   TEST 012 seemed dead - so the bottom of the range is left in as
//   a usable "almost nothing" rather than clamped away.
//
//   THREE TUNED VALUES ARE NOW UNSAVED: backlight, strength and
//   length, all back to defaults on reboot. The AT24C32 at 0x57 is
//   the place for them and is still unused. Not built without
//   being asked for.
//
// WHAT CHANGED IN TEST 017 vs TEST 016
//   A REAL BUG, MINE. The day of week was one short - it said Thu
//   for Friday 4 September 2026. Zeller itself was right and
//   returned h=6, which IS Friday. The mapping from h to the
//   DS3231's 1..7 was wrong: ((h + 5) %% 7) + 1 instead of
//   ((h + 6) %% 7) + 1. Checked against 1 January 2000, a Saturday,
//   which now comes out Sat. The wrong day is already written into
//   the chip, so the clock has to be set once more after flashing.
//
//   Removed, as asked: the 1024 x 600 label, the seconds in the
//   time, the century in the year, and the I2C line at the bottom
//   of the home screen.
//
//   THE ONE SECOND I2C SCAN IS ALSO GONE, not just its label. It
//   existed to feed that line. Leaving it running to write to
//   nothing would burn bus time every second for no reader. The
//   serial commands survive and now do the scan on demand:
//       i   the named table
//       s   full sweep 0x08..0x77
//
//   FOUR SCREENS: Massage, Radio, Air conditioner, Fan.
//
//   THE HEBREW STRINGS ARE STORED REVERSED. They are copied
//   verbatim from TEST 081, where the letters are written back to
//   front on purpose because LVGL has no bidirectional text and
//   would otherwise draw Hebrew left to right. Do not "fix" them in
//   an editor - they are correct as they stand and will break if
//   reordered.
//
//   NONE OF THESE SCREENS CONTROLS ANYTHING YET, and this is the
//   honest state of it. There is no RS-485 bus, no bedbox firmware
//   and no IR transmitter on this panel. Every control changes a
//   variable and prints to serial. They are real interfaces waiting
//   for a transport, not simulations pretending to work.
//
//   THE RADIO STATION LIST IS A PLACEHOLDER except Galgalatz, which
//   is the one station with a URL verified end to end on audionode.
//   The other seven are names on tiles. Replace them when the real
//   list exists.
//
//   THE AC SCREEN SHOWS THE ROOM TEMPERATURE FROM THE SHT3x, so the
//   target can be set against something real rather than guessed.
//
// WHAT CHANGED IN TEST 016 vs TEST 015
//   A settings screen, ported from buildSettings() in TEST 081.
//   Two tabs for now - Clock and Display - with room for Massage,
//   Files and About later, exactly as the old one had.
//
//   FONTS: 26 is the largest available. The Waveshare lv_conf.h
//   enables only 12, 14, 16 and 26, and the vendor file stays
//   untouched by decision. The old screen used 40 for the digits
//   and 28 for the +/- signs; both drop. The BUTTONS are still
//   large - a touch target is set by its size, not its font - so
//   the screen is no harder to use, only less dramatic.
//
//   24 HOUR, so the screen and the driver speak the same language.
//   The old screen was 12 hour with an AM/PM toggle, which meant
//   converting in two directions around a register whose bit 6
//   already encodes the mode. One representation, no conversion.
//
//   THE TABVIEW IS PAINTED BY HAND. This is not decoration. LVGL's
//   default theme leaves a tabview and its bar near white, which on
//   this screen at night is a slab of light in a dark bedroom. TEST
//   073 hit this on the old panel; the same treatment is carried
//   over.
//
//   THE FIELDS SEED FROM THE CHIP on every entry to the screen, via
//   LV_EVENT_SCREEN_LOAD_START. Seeding once at boot would mean
//   opening settings later showed stale numbers and pressing Set
//   would quietly move a correct clock backwards.
//
//   THE YEAR IS CLAMPED TO 2000-2099 because the DS3231 stores two
//   digits and a century bit that this driver does not use. A year
//   outside that range cannot round trip through the register.
//
//   NOT PERSISTENT. The backlight slider takes effect immediately
//   but is not stored, so it returns to the default on reboot. The
//   AT24C32 at 0x57 is the obvious place for it and is still
//   unused. Left out on purpose rather than added unasked.
//
//   HAPTIC ON THE TAB BUTTONS DOES NOT FIRE. The buttons this file
//   creates carry EVENT_BUBBLE and reach the screen handler; the
//   ones LVGL builds inside the tabview do not. Known, small, and
//   not worth reaching into tabview internals for.
//
// WHAT CHANGED IN TEST 015 vs TEST 014
//   Half the minute lines said sht FAIL (fetch NACK) and the other
//   half read correctly, alternating. My bug, introduced in TEST
//   013.
//
//   A NACK ON FETCH IN PERIODIC MODE MEANS "NO NEW MEASUREMENT
//   YET". It is documented behaviour, not an error. The sensor is
//   in 0.5 mps - one measurement every two seconds - and the data
//   is cleared once read. shtRead() runs every second. So every
//   other fetch necessarily lands between measurements and is
//   correctly not acknowledged.
//
//   TEST 013 treated that as a failure: it cleared the reading, set
//   shtOK false, and counted toward a rearm that was never needed.
//   The visible cost was the climate line on screen flickering to
//   -- and back every other second.
//
//   NOW: a NACK keeps the last good value and changes nothing. The
//   reading is only declared stale after SHT_STALE_MS with no
//   successful fetch, and only then does the rearm fire. That is a
//   real fault - a sensor knocked out of periodic mode - as opposed
//   to the sensor working exactly as configured.
//
//   The values themselves were never in doubt: 25.7 C drifting down
//   to 25.24 over twenty minutes, 59 %RH throughout, and the DS3231
//   tracking within half a degree.
//
// WHAT CHANGED IN TEST 014 vs TEST 013
//   The tick was felt but barely. Turned up to maximum.
//
//   DURATION MATTERED MORE THAN DUTY, and this is the real fault
//   in TEST 012. A coin ERM needs 50 to 80 ms to reach full speed.
//   The pulse was 40 ms end to end, so it FINISHED BEFORE THE MOTOR
//   GOT THERE. What reached the finger was the spin up, never the
//   vibration. Duration is now 150 ms, which is past full speed
//   with room to be felt.
//
//   Duty is 100 percent. At 36 mA measured this costs the 5 V rail
//   nothing. The motor's rated voltage is not printed on it, so
//   full rail continuously would be a gamble - but at 150 ms per
//   touch the duty cycle over any minute is a fraction of a
//   percent, and brush wear does not accumulate at that rate.
//
//   THE KICK IS GONE. It existed to break stiction before dropping
//   to 70 percent. At 100 percent there is nothing to drop to, so
//   it became a no-op.
//
//   LIVE TUNING, same pattern as n/f/b:
//       v<0-100>   strength
//       h<ms>      pulse length
//   Feel is not a thing to guess at from here, and rebuilding to
//   change one number wastes your afternoon. Both print what they
//   land on so the final values can be written into the file.
//
//   IF IT IS STILL WEAK, THE FIRMWARE IS NO LONGER THE LIMIT. This
//   is as hard as the part goes. Past here it is mounting: a motor
//   on foam, on soft tape, or hanging on its wires puts its energy
//   into moving itself instead of the panel.
//
// WHAT CHANGED IN TEST 013 vs TEST 012
//   The SHT3x was NEVER BROKEN. TEST 012 printed sht 0.00 C once
//   and I called it a systematic failure. It was not. The minute
//   line fires on the first tick where the RTC reads, and on that
//   tick the measurement command has only just been sent - the
//   collection happens on the NEXT tick. So the first line can only
//   ever print a failure. Every line after it was correct: 26.7 C,
//   56 %RH, and the DS3231 converging to within 0.2 C of it.
//
//   I drew a conclusion from one sample taken at the one moment it
//   could not have worked. The atomic fetch and the self rearming
//   below are worth keeping as robustness, but they fixed nothing,
//   and calling them a fix would have been false.
//
// WHAT CHANGED IN TEST 012 vs TEST 011
//   TEST 012 ran. BH1750 reads, DS3231 answers, backlight and
//   touch fine. Two things were wrong.
//
//   1. monitor_filters had "echo", which is not a real filter.
//      PlatformIO printed "Skipping unknown filters" and ignored
//      it. My mistake. Removed. Typing stays blind; send_on_enter
//      still buffers the line and sends it on Enter.
//
//   2. THE SHT3x READ FAILED EVERY TIME, and the printout proved
//      it rather than merely suggesting it: the value was 0.00 C.
//      The conversion is -45 + 175 * raw/65535, so even an all
//      zero reading prints -45.00. A clean 0.00 can only come from
//      the shtOK ? value : 0.0f branch. The read never succeeded.
//
//      HYPOTHESIS, labelled as one: the presence scanner killed it.
//      It probes 0x44 once a second - a START, an address, a STOP,
//      no command. TEST 012 left the sensor holding a single shot
//      result between two one second ticks, and a foreign write in
//      that gap discards it. It also explains why the BH1750
//      survives: its state is a running mode, not a one shot result
//      that can be thrown away.
//
//      THE FIX DOES NOT RELY ON THAT HYPOTHESIS. The sensor now
//      runs in periodic mode and the result is fetched in ONE
//      atomic transaction - command and read joined by a repeated
//      START, which no other transfer can get between. There is no
//      longer any state that has to survive from one bus access to
//      the next, so there is nothing left to lose.
//
//      0.5 measurements per second, high repeatability. Periodic
//      mode also drops self heating below what single shot on
//      demand was doing.
//
//      AND IT REARMS ITSELF. Five consecutive failures resend the
//      periodic mode command. If anything ever does knock the
//      sensor out of it, the panel recovers instead of showing --
//      until the next reboot.
//
//      DIAGNOSTICS ADDED. Two different failures - a NACK and a bad
//      checksum - printed identically before. Now the minute line
//      names which one happened.
//
// WHAT CHANGED IN TEST 012 vs TEST 011
//   A coin vibration motor on GPIO 6 gives a short tick on every
//   touch, anywhere on the screen.
//
//   MEASURED, not assumed: 22 mA at 3.3 V, 36 mA at 5 V, both with
//   the motor spinning. Under 1 mA on IN, which is a MOSFET gate,
//   not a bipolar base. 535 mV across the motor pads in diode mode,
//   so the flyback diode is already on the module. Nothing external
//   is needed. VCC comes off the same 5 V that feeds the board, so
//   the ground is common by construction.
//
//   LEDC, NOT digitalWrite. Not for the current - 36 mA is nothing.
//   For control. The motor's rated voltage is not printed anywhere
//   and the AliExpress text is machine generated and demonstrably
//   wrong about the part, so running it at a duty cycle instead of
//   a rail is the honest way to avoid committing to a number nobody
//   stated. 70 percent of 5 V is about the 3.3 V that already
//   worked.
//
//   ARDUINO CORE 3.x LEDC API. ledcSetup and ledcAttachPin are
//   gone. It is ledcAttach(pin, freq, bits), and ledcWrite takes
//   the PIN, not a channel number. Passing a channel silently
//   writes to the wrong pin.
//
//   20 kHz, above hearing. A motor driven in the audible band
//   whines, and this sits on a headboard.
//
//   THERE IS A STARTING KICK. An ERM will not begin to turn at 70
//   percent from standstill - static friction plus an off-centre
//   weight needs more. So the pulse opens at 100 percent for 12 ms
//   and then drops to 70 for the rest. Without it the tick feels
//   late and weak, or does not happen at all. Set HAPTIC_KICK_MS to
//   0 to remove it.
//
//   THE PULSE IS A TIMER, NOT A DELAY. Same reason the SHT3x read
//   is split across ticks: a delay inside the LVGL task can show as
//   a dropped frame on an RGB panel. The touch returns immediately
//   and the motor stops on its own.
//
//   ONE HANDLER FOR THE WHOLE SCREEN. Every tile gets
//   LV_OBJ_FLAG_EVENT_BUBBLE, so a press on a tile travels up to
//   the screen, and a press on bare background lands there
//   directly. One callback covers both, and every tile added later
//   is covered without touching this code again.
//
//   LV_EVENT_PRESSED, not CLICKED. Pressed fires the moment the
//   finger lands. Clicked waits for the release. Feedback that
//   arrives on release is not feedback.
//
//   GPIO 6 FLOATS DURING RESET, so the motor twitches at every
//   boot. Left in deliberately - it is a usable sign that the
//   system came up. It is not under firmware control: it also
//   happens on a watchdog reset or a brownout recovery, so a boot
//   loop would buzz in a loop. A 10k from IN to GND removes it.
//
// NOT YET COMPILED, NOT YET RUN ON HARDWARE.
//
// WHAT CHANGED IN TEST 011 vs TEST 010
//   TEST 010 proved the bus on hardware. Answering: 0x24 IO
//   expander, 0x5D touch, 0x44 SHT3x, 0x68 DS3231, 0x57 AT24C32.
//   The presence scan stays exactly as it was and still runs.
//
//   Added: real drivers for the RTC and the climate sensor, a
//   reading line across the top, and a way to set the clock.
//
//   BH1750 DID NOT ANSWER. Neither 0x23 nor 0x5C. Its driver is
//   written anyway and it degrades to "--". Plug the module in and
//   it starts reading with no code change.
//
//   THE OSCILLATOR STOP FLAG IS CHECKED, and this matters. The
//   DS3231 sets bit 7 of register 0x0F when the oscillator has
//   stopped - a dead backup cell, or a first power-up. The time
//   registers still return a number after that, and the number is
//   meaningless. Without the check the panel shows a confident
//   wrong time. With it, it says CLOCK NOT SET and waits.
//
//   THE SHT3x READ IS SPLIT ACROSS TWO TICKS. A single-shot high
//   repeatability measurement needs about 15 ms between the
//   command and the result. Sleeping for it inside the LVGL timer
//   would stall the task and can show as a dropped frame on an RGB
//   panel. So one tick sends the command, the next tick collects
//   it. The sensor holds the result until read. Nothing blocks.
//
//   CLOCK STRETCHING IS NOT USED for the same class of reason: it
//   would hold SCL low, and the touch controller is on that wire.
//
//   READING EVERY 5 SECONDS, NOT EVERY SECOND. The SHT3x heats
//   itself slightly when measuring. At high repeatability, once a
//   second, that self-heating is measurable in a reading that is
//   supposed to be room temperature. Five seconds is far more than
//   a bedroom needs.
//
//   SETTING THE TIME IS OVER SERIAL, NOT ON SCREEN. Deliberate
//   order: prove the driver against real registers first, then put
//   an interface on a thing that is known to work. The on-screen
//   setter comes back afterwards.
//       T2026-09-03 13:45:00
//   Day of week is computed, not typed. The command also clears
//   the oscillator stop flag, because a fresh set is exactly the
//   moment the old warning stops being true.
//
//   The serial line buffer was 8 characters. A time string is 19.
//   Raised to 40.
//
//   THE DS3231 HAS ITS OWN TEMPERATURE SENSOR and it is shown on
//   serial next to the SHT3x. It is only good to about 3 degrees
//   and it sits on a warm board, so it is not the room reading -
//   it is a cross-check. Two independent sensors disagreeing by
//   fifteen degrees means something is wrong with one of them.
//
//   0x57 IS 4 KB OF FREE EEPROM on the RTC module, and it survives
//   a flash erase. Noted as an asset. Not used yet.
//
// WHAT CHANGED IN TEST 010 vs TEST 009
//   The home screen is untouched. Same eight tiles, same 200 px
//   artwork, same positions, same live dim and backlight tuning.
//   Nothing about the layout moved.
//
//   What is added is a presence line above the status line, and a
//   named table on serial. This is the first time the sensors hang
//   on the bus, and an address that answers proves the wiring
//   before a single driver exists to be blamed.
//
//   MODULES ON HAND, confirmed from photographs of the boards:
//     DS3231M RTC   OPEN-SMART, CR1220 fitted      expect 0x68
//     SHT3x         purple breakout, SHT3x marked  expect 0x44
//     BH1750        GY-302 V322                    expect 0x23
//     one blue 7-pin board, ADD RST ALE SDA SCL VCC GND,
//       chip marking unreadable in the photograph - the scan
//       is what identifies it, not a guess
//
//   0x24 and 0x5D MUST appear. They are the IO expander and the
//   touch controller, both already on this bus and both working.
//   If either goes missing the fault is the bus itself, not a
//   sensor, and nothing further should be built until it is back.
//
// WHY THE SCAN RUNS INSIDE THE LVGL TASK
//   Touch is read from the LVGL task. Scanning from loop() would
//   put two tasks on I2C_NUM_0 at once. Everything that touches
//   the bus now happens in one place, in one order. The serial
//   sweep command sets a flag; the timer does the work.
//
// WHY IT PROBES AND DOES NOT WRITE
//   A write would change state. 0x00 to a BH1750 is Power Down,
//   and a stray byte to the GT911 can leave its register pointer
//   somewhere unexpected and cost you the touchscreen.
//
// WHY NOT DEV_I2C_Read_Byte
//   Every helper in lib/i2c is wrapped in ESP_ERROR_CHECK. A NACK
//   from an empty address is normal and expected during a scan,
//   but ESP_ERROR_CHECK turns it into a panic - which would mean a
//   reboot loop on every pass. i2c_master_probe is called directly
//   and its return value is checked.
//
// THE BUS IS BORROWED, NEVER RE-CREATED
//   DEV_I2C_Init() calls i2c_new_master_bus and is already called
//   once inside touch_gt911_init(). Calling it again panics. The
//   handle is taken from the global that i2c.cpp keeps.
//
// NOT YET COMPILED, NOT YET RUN ON HARDWARE.
//
// WHAT THIS IS
//   The home screen from the old panel, laid out for the new one.
//   Tiles and touch only. No sensors, no clock, no RS485, no photos.
//   Look at it, decide whether the layout is right, and only then
//   port the deeper screens.
//
// WHY 4 x 2 AND NOT 3 x 2
//   The old grid was three 200 px tiles across, 22 px apart, starting
//   at x = 78. That is 644 px of tiles inside 800, leaving 78 px each
//   side.
//
//   Four of the same tiles is 866 px inside 1024, leaving 79 px each
//   side. Within one pixel of the old margin. So the wider screen
//   buys a whole extra column without changing a single dimension,
//   and every icon stays at its native 200 x 200 - no scaling, no
//   softening.
//
//   Vertically 600 - 416 = 184 spare, split as a taller status strip
//   above and breathing room below.
//
// THE TWO NEW SLOTS
//   Position 3 on the top row is the ceiling fan. Its 433 MHz
//   protocol is already decoded: protocol 2, 29 bits, address
//   0x3D755, fourteen buttons captured.
//
//   And it turns out the artwork already exists. fan_img.h was
//   sitting in include/ - 200x200, cut from a photograph of the
//   actual fan in the room. It was made for TEST 082, the delivery
//   that was never pushed and was assumed lost. The code went, the
//   picture survived. So the fan tile is a real photograph like the
//   other five, not a placeholder symbol.
//
//   Position 3 on the bottom row is left free on purpose.
//
// WHAT CHANGED vs TEST 008
//   A single dim value was applied to every tile whatever its state,
//   so on and off differed only by the artwork swap. Feedback from
//   the screen: keep the lit state as it is and push the unlit state
//   further down, so the difference is obvious at a glance rather
//   than something you have to read.
//
//   So the dim level is now a pair - dimOn and dimOff - and the tile
//   background darkens as well when unlit. Two effects stacking:
//   the picture recedes and the panel behind it recedes with it.
//
//   Both are tunable live, same as the backlight:
//       n<v>   dim when ON    0..255
//       f<v>   dim when OFF   0..255
//       b<v>   backlight      0..100
//
//   Defaults are a starting point only. Real calibration waits for
//   the BH1750 - a value picked by eye in daylight is wrong at night,
//   and with the sensor in place brightness becomes a curve rather
//   than a number. No point doing it twice.
//
// WHAT CHANGED IN TEST 008 vs TEST 007  -  A HARDWARE FACT WORTH KEEPING
//   The backlight control is INVERTED. Measured, not guessed:
//   b0 gave a bright, readable screen and b100 gave a dark one.
//
//   IO_EXTENSION_Pwm_Output() does not take brightness. It takes how
//   much to DIM. So every build from TEST 003 to TEST 007 called it
//   with 100 at startup and ran the panel at full dim, which is why
//   even d0 looked washed out. The artwork was never the problem and
//   neither was the dim value - the screen was simply turned down.
//
//   From here the code inverts it: applyBacklight(100) writes 0 to
//   the expander and gives full brightness. b100 is bright, b0 is
//   off, which is what anyone would expect.
//
//   Leave this inversion in place. It is a property of the board,
//   and it will silently break every screen that gets ported if it
//   is ever removed.
//
// WHAT CHANGED IN TEST 007 vs TEST 006
//   Dim 255 gave a black screen, dim 0 still looked dull. That rules
//   the dimming out: 0 means no darkening at all, so if the artwork
//   is still weak at 0 the problem was never the dim value.
//
//   The remaining suspect is the backlight. TEST 002 proved the
//   IO expander drives it - the slider visibly changed brightness.
//   From TEST 003 on it was set once in setup() and never again,
//   with no way to check or change it. So it is now a live command
//   too, and the two are separated:
//       d<n>   tile dim      0..255
//       b<n>   backlight     0..100
//   Change one, watch, change the other. Whichever moves the picture
//   is the one that matters.
//
//   Default dim is now 10, chosen from the live tuning.
//
//   The monitor also does not echo what is typed. That is a
//   platformio.ini setting, not code: monitor_filters = echo.
//
// WHAT CHANGED IN TEST 006 vs TEST 005
//   TEST 005 ran and all eight tiles came up, but the artwork was
//   almost black. TILE_DIM_OPA was 110, a value tuned on the old
//   800x480 Guition panel. This screen has a different backlight and
//   a different panel, so the number did not carry over. Carrying it
//   was reasonable; not checking it was not.
//
//   Rather than guess a new value and rebuild five times, the dim
//   level is now adjustable from the serial monitor while the screen
//   is running. Type a number, watch the tiles change, and when it
//   looks right that number goes into the code as the new default.
//
//   Default lowered from 110 to 40 as a starting point.
//
// WHAT CHANGED IN TEST 005 vs TEST 004
//   TEST 004 would not compile: lv_font_montserrat_40 and _20 are not
//   built. The Waveshare lv_conf.h enables only 12, 14, 16 and 26.
//   The old panel had its own lv_conf.h with more sizes turned on,
//   and I wrote against that from memory instead of reading the one
//   actually in use.
//
//   So 40 becomes 26 and 20 becomes 16. Their lv_conf.h is left
//   untouched on purpose: it is a config file and editing it is
//   legitimate, but every edit to the vendor port layer is one more
//   thing to remember and restore if it is ever updated. Fitting our
//   code to what exists costs nothing here.
//
//   To get bigger symbols later, set LV_FONT_MONTSERRAT_40 to 1 in
//   lib/lv_conf.h. Not needed for this.
//
// WHAT IS DELIBERATELY MISSING
//   Every tile prints to serial instead of acting. Nothing is wired
//   to the bus yet, and a tile that silently does nothing is worse
//   than one that says so.
//
// NOT YET RUN ON HARDWARE.
//
// ============================================================

#include <Arduino.h>
#include <math.h>   // log10f, for the logarithmic lux mapping
#include "lvgl_port.h"
#include "rgb_lcd_port.h"
#include "io_extension.h"
#include "i2c.h"        // DEV_I2C_Port, driver/i2c_master.h

#include "tile_img.h"       // img_bed_off/on, img_radio_off/on,
                            // img_ac_off/on, img_shade_open/closed
#include "lamp_img.h"       // img_lamp
#include "fan_img.h"        // img_fan - recovered from TEST 082
#include "font_hebrew.h"     // font_hebrew_28
#include "alarm_img.h"      // img_alarm_on / img_alarm_off
#include "boot_photo.h"     // BOOT_SHEMI_JPG / BOOT_IRA_JPG
#include <JPEGDEC.h>

// 1 = this panel, Shemi. 2 builds Ira's from the same file and
// shows her photograph, so the picture on screen tells you which
// board you just flashed.
#define PANEL_ID 1
#define RS485_RX_PIN 15
#define RS485_TX_PIN 16
#define RS485_BAUD   115200
#define RS485        Serial1

static constexpr uint8_t NODE_SHEMI  = 1;
static constexpr uint8_t NODE_IRA    = 2;
static constexpr uint8_t FRAME_START = 0xA5;
static constexpr uint8_t TYPE_TIME   = 0x10;
static constexpr uint8_t TYPE_ACK    = 0x11;

struct TimeFrame {
  uint8_t start;
  uint8_t src;
  uint8_t dst;
  uint8_t type;
  uint8_t seqLo;
  uint8_t seqHi;
  uint8_t yearLo;
  uint8_t yearHi;
  uint8_t month;
  uint8_t day;
  uint8_t hour;
  uint8_t minute;
  uint8_t second;
  uint8_t crc;
};

static_assert(sizeof(TimeFrame) == 14, "TimeFrame must be exactly 14 bytes");

static uint32_t rsGoodTimes = 0;
static uint32_t rsBadFrames = 0;
static uint32_t rsReplies   = 0;

static uint8_t rsFrameCrc(const TimeFrame &f) {
  const uint8_t *p = reinterpret_cast<const uint8_t *>(&f);
  uint8_t c = 0;
  for (size_t i = 0; i < sizeof(TimeFrame) - 1; ++i) c ^= p[i];
  return c;
}

static uint16_t rsFrameSeq(const TimeFrame &f) {
  return uint16_t(f.seqLo) | (uint16_t(f.seqHi) << 8);
}

static uint16_t rsFrameYear(const TimeFrame &f) {
  return uint16_t(f.yearLo) | (uint16_t(f.yearHi) << 8);
}

static TimeFrame rsMakeAck(uint16_t seq) {
  TimeFrame f{};
  f.start = FRAME_START;
  f.src = NODE_IRA;
  f.dst = NODE_SHEMI;
  f.type = TYPE_ACK;
  f.seqLo = uint8_t(seq & 0xFF);
  f.seqHi = uint8_t((seq >> 8) & 0xFF);
  f.crc = rsFrameCrc(f);
  return f;
}

static void rsSendFrame(const TimeFrame &f) {
  RS485.write(reinterpret_cast<const uint8_t *>(&f), sizeof(f));
  RS485.flush();
}

static void handleBedboxLevelFeedback(uint8_t bedId, uint8_t cmd,
                                      uint8_t zone, uint8_t level);
static bool rsReadFrame(TimeFrame &out) {
  static uint8_t buf[sizeof(TimeFrame)];
  static size_t pos = 0;

  // TEST067: legacy BedBox feedback lives beside the A5 TIME/ACK stream.
  // Only valid {bedId,20,zone,level} frames are acted on.
  static uint8_t rpt[4] = {0, 0, 0, 0};
  static size_t rptPos = 0;

  while (RS485.available()) {
    const uint8_t b = uint8_t(RS485.read());

    if (pos == 0) {
      if (b != FRAME_START) {
        // TEST067: collect non-A5 bytes as possible 4-byte BedBox feedback.
        rpt[rptPos++] = b;

        if (rptPos == 4) {
          if ((rpt[0] == 1 || rpt[0] == 0) &&
              rpt[1] == 20 &&
              rpt[2] < 4 &&
              rpt[3] <= 100) {
            handleBedboxLevelFeedback(rpt[0], rpt[1], rpt[2], rpt[3]);
            rptPos = 0;
          } else {
            // Sliding-window resync: keep the last 3 bytes.
            rpt[0] = rpt[1];
            rpt[1] = rpt[2];
            rpt[2] = rpt[3];
            rptPos = 3;
          }
        }
        continue;
      }

      // An A5 frame starts here. A partial legacy candidate cannot span it.
      rptPos = 0;
      buf[pos++] = b;
      continue;
    }

    buf[pos++] = b;

    if (pos == sizeof(TimeFrame)) {
      memcpy(&out, buf, sizeof(out));
      pos = 0;
      return true;
    }
  }
  return false;
}

static bool rsTimeFieldsValid(const TimeFrame &f) {
  const uint16_t y = rsFrameYear(f);
  return y >= 2000 && y <= 2099 &&
         f.month >= 1 && f.month <= 12 &&
         f.day >= 1 && f.day <= 31 &&
         f.hour <= 23 && f.minute <= 59 && f.second <= 59;
}

#define TEST_NUMBER 74

// ------------------------------------------------------------
// Layout. Every number here is derived, not guessed - see the
// header note on why four columns fit exactly.
// ------------------------------------------------------------

#define SCREEN_W    1024
#define SCREEN_H     600

#define TILE_SZ      200
#define TILE_GAPX     22
#define TILE_GAPY     16
#define TILE_COLS      4
#define TILE_ROWS      2

// (1024 - (4*200 + 3*22)) / 2 = 79
#define TILE_X0       79
// status strip above, a little air below
#define TILE_Y0      108

// How far the tile artwork is pulled toward black, 0..255. Carried
// over from TEST 080 unchanged: 110 takes the glare off the white
// bed without making the icons hard to read.
// Runtime, not a #define, so it can be tuned live. 0 is the original
// artwork, 255 is a black square.
// Lit tiles keep the artwork close to original. Unlit tiles sink
// well back. The gap between the two is the whole point.
#define DIM_ON_DEFAULT   10
#define DIM_OFF_DEFAULT 120
static uint8_t dimOn  = DIM_ON_DEFAULT;
static uint8_t dimOff = DIM_OFF_DEFAULT;

// The panel behind the artwork moves too, so an unlit tile recedes
// twice over.
#define TILE_BG_ON  0x181C22
#define TILE_BG_OFF 0x0C0F13

// Backlight, 0..100, straight through the IO expander at 0x24.
#define BACKLIGHT_DEFAULT 100
static uint8_t backlight = BACKLIGHT_DEFAULT;

// ---- automatic brightness ----
//
// AUTO_LUX_LO / HI are the ends of the mapped range in lux. 1 lx is
// a dark room, 1000 lx is a bright one indoors; beyond that the
// screen is already at maximum and more light changes nothing.
#define AUTO_LUX_LO      1.0f
#define AUTO_LUX_HI      1000.0f
#define AUTO_TICK_MS     100     // the controller's own timer
#define AUTO_DEADBAND    1       // points; below this, do not move

// One slider drives both halves of the response. Speed 1 is the
// slow, smooth behaviour; speed 10 crosses the whole range in about
// a second, which is as fast as a 120 ms sensor conversion allows.
#define AUTO_SPEED_MIN   1
#define AUTO_SPEED_MAX   10
static uint8_t autoSpeed = 6;

// ---- screensaver ----
// Here rather than with the screensaver code, because the EEPROM
// record below has to see them and it comes first in the file.
// 0 means never.
// Nine steps, not a free slider. Nobody wants a screensaver delay
// of seven minutes and twenty three seconds, and a free slider
// makes landing exactly on five minutes a fiddle.
static const uint32_t kSaverOpts[9] = {
  0, 15000UL, 30000UL, 60000UL, 120000UL,
  300000UL, 600000UL, 1200000UL, 1800000UL
};
static const char *kSaverNames[9] = {
  "Never", "15 sec", "30 sec", "1 min", "2 min",
  "5 min", "10 min", "20 min", "30 min"
};
// The five entry table byte 12 was written against, kept only so an
// older record can be translated instead of thrown away.
static const uint8_t kSaverLegacy[5] = { 0, 2, 3, 5, 6 };

static uint8_t  saverIdx     = 5;          // 5 minutes
static uint32_t saverAfterMs = 300000UL;

// Was a constant in the source until now, which meant the one
// number deciding how much light sits beside a sleeping head could
// only be changed by rebuilding.
static uint8_t  saverBright  = 8;          // percent

// These three live here too, and for the same reason: the touch
// handler and the brightness controller both use them and both come
// long before the screensaver code in this file.
// Stored as "once" rather than "repeat". Bit 3 of the flags byte
// was always zero before, and every alarm until now repeated daily -
// so zero has to keep meaning every day, or every saved alarm would
// quietly become once-only on the first boot after flashing.
static bool     alarmOnce     = false;

// ---- radio sleep timer ----
// sleepEnd is a millis() deadline, 0 meaning off. Compared by
// subtraction, never by >=, because millis() wraps after about 49
// days and a headboard panel will cross that.
static uint8_t  sleepMin = 30;
static uint32_t sleepEnd = 0;

static bool     saverOn       = false;
static uint32_t lastTouchMs   = 0;
static uint8_t  blBeforeSaver = 100;

// ---- clock display ----
// TEST073: display is always 12-hour AM/PM. The DS3231 itself stays
// in 24-hour form, so storage and bus time remain unambiguous.
static bool use12h = true;

// h is 0..23. Returns 1..12 and sets suffix to "AM" or "PM".
// Written out rather than using h % 12, which maps both midnight
// and noon to zero and prints "0:15 AM".
static uint8_t to12(uint8_t h, const char **suffix) {
  *suffix = (h < 12) ? "AM" : "PM";
  if (h == 0)  return 12;      // midnight
  if (h == 12) return 12;      // noon
  return (uint8_t)(h % 12);
}

// ---- touch feedback, tunable ----
// Declared here rather than beside the motor code so the EEPROM
// record below can see every stored value in one place.
#define HAPTIC_DUTY_PCT  100     // full rail; 36 mA measured, the rail shrugs
#define HAPTIC_BODY_MS   150     // past the 50-80 ms an ERM needs to spin up
static uint8_t  hapDutyPct = HAPTIC_DUTY_PCT;
static uint16_t hapLenMs   = HAPTIC_BODY_MS;

static inline float autoAlpha() { return 0.04f * autoSpeed; }   // 0.04 .. 0.40
static inline int   autoStep()  { return autoSpeed; }           // points per tick

static bool    autoBright = true;
static uint8_t blMin      = 12;
static uint8_t blMax      = 100;
static float   luxSmooth  = -1.0f;   // negative = not seeded yet

// Hebrew is stored pre-reversed in the font header, so the string is
// written here in visual order and needs no bidi engine.
#define HEB_BEDROOM  "\xD7\x94\xD7\xA0\xD7\x99\xD7\xA9\x20\xD7\xA8\xD7\x93\xD7\x97"
#define TITLE_HOME   "BG " HEB_BEDROOM

// ------------------------------------------------------------

static lv_obj_t *scrHome     = NULL;
static lv_obj_t *scrSettings = NULL;

// These two live on the settings screen but are refreshed by
// sensorTick, which is defined further up the file - so they are
// declared here rather than beside the rest of the settings widgets.
static lv_obj_t *lblNowTime  = NULL;   // live clock, Clock tab
static lv_obj_t *lblLuxLive  = NULL;   // live lux, Display tab
static lv_obj_t *lblAcRoom   = NULL;   // live room temperature, AC screen

// The other screens. Declared here because the home tile handlers
// further down have to load them, and they are built much later.
static lv_obj_t *scrMassage  = NULL;
static lv_obj_t *scrRadio    = NULL;
static lv_obj_t *scrAC       = NULL;
static lv_obj_t *scrFan      = NULL;
static lv_obj_t *scrAlarm    = NULL;

// ---- alarm ----
//
// Everything is minute of day, 0..1439. Snooze then crosses
// midnight with no special case: 23:55 plus nine is 00:04 and the
// modulo does it.
#define ALARM_SNOOZE_MIN  9
#define ALARM_GIVEUP_MS   (20UL * 60UL * 1000UL)  // stop buzzing at an empty room
#define ALARM_RING_EVERY  2000UL                  // ms between ring pulses
#define ALARM_RING_PCT    100                     // ignores the touch settings
#define ALARM_RING_MS     400

static bool     alarmOn      = false;
static int      alarmMin     = 7 * 60;   // 07:00
static int      snoozeUntil  = -1;       // minute of day, -1 = none
static bool     ringing      = false;
static uint32_t ringStart    = 0;
static uint32_t lastRingPulse= 0;
static int      lastMinSeen  = -1;
static bool     alarmFirstTick = true;
static lv_obj_t *lblStatus   = NULL;
static lv_obj_t *lblClock    = NULL;   // time, top centre
static lv_obj_t *lblClimate  = NULL;   // temperature, humidity, lux

// ------------------------------------------------------------
// I2C presence scan
//
// The bus already exists. DEV_I2C_Init() ran inside
// touch_gt911_init() and stored the handle in a file-scope global
// in lib/i2c/i2c.cpp. It is borrowed here. Calling DEV_I2C_Init()
// a second time would call i2c_new_master_bus twice and panic.
// ------------------------------------------------------------
extern DEV_I2C_Port handle;          // defined in lib/i2c/i2c.cpp

struct Known {
  uint8_t     addr;
  const char *name;
  bool        required;   // must answer, or the bus itself is broken
};

// Only these are polled every second. A full 0x08..0x77 sweep is
// 112 transactions and would stall the LVGL task long enough to
// drop a frame on an RGB panel. Type 's' on serial for that.
static const Known kKnown[] = {
  { 0x14, "GT911 touch alt",  false },
  { 0x23, "BH1750 lux",       false },
  { 0x24, "IO expander",      true  },
  { 0x38, "AHT20",            false },
  { 0x44, "SHT3x",            false },
  { 0x45, "SHT3x alt",        false },
  { 0x57, "AT24C32 eeprom",   false },
  { 0x5A, "DRV2605L haptic",  false },
  { 0x5C, "BH1750 alt",       false },
  { 0x5D, "GT911 touch",      true  },
  { 0x68, "DS3231 rtc",       false },
  { 0x76, "BMx280",           false },
  { 0x77, "BMx280 alt",       false },
};
static const int kKnownCount = sizeof(kKnown) / sizeof(kKnown[0]);

static bool present[kKnownCount];
static bool scanReady    = false;   // one pass has completed

// A probe is an address byte and a stop. Nothing is written, so no
// device changes state.
static bool probeAddr(uint8_t addr) {
  if (handle.bus == NULL) return false;
  return i2c_master_probe(handle.bus, addr, 50) == ESP_OK;
}

static void printTable() {
  Serial.println();
  Serial.println("=== I2C ===");
  for (int i = 0; i < kKnownCount; i++) {
    Serial.printf("  0x%02X  %-18s %-6s %s\n",
                  kKnown[i].addr,
                  kKnown[i].name,
                  present[i] ? "FOUND" : "--",
                  kKnown[i].required
                      ? (present[i] ? "(must be)" : "(MISSING - BUS FAULT)")
                      : "");
  }
  Serial.println();
}

// Full sweep. Runs only on request, only from the LVGL task.
static void fullSweep() {
  Serial.println();
  Serial.println("=== full sweep 0x08..0x77 ===");
  int n = 0;
  for (uint8_t a = 0x08; a <= 0x77; a++) {
    if (probeAddr(a)) { Serial.printf("  0x%02X\n", a); n++; }
  }
  Serial.printf("  %d device(s)\n\n", n);
}

// The scan no longer runs on a timer. It existed to feed a label on
// the home screen, and that label is gone; a scan writing to nobody
// would just take bus time once a second. It is now on demand from
// serial - i for the named table, s for a full sweep - and runs
// inside the LVGL task like everything else that touches the bus.
static bool scanWanted  = false;   // set from serial, served by sensorTick
static bool sweepWanted = false;

static void i2cScanNow(bool sweep) {
  if (sweep) fullSweep();
  for (int i = 0; i < kKnownCount; i++) present[i] = probeAddr(kKnown[i].addr);
  scanReady = true;
  printTable();
}

// ------------------------------------------------------------
// Device handles.
//
// One handle per sensor, created once. Creating a handle for a
// device that is not plugged in is harmless - it is only a config
// entry. The reads fail and the display shows "--".
//
// 0x24 and 0x5D are deliberately NOT added here. They already have
// handles owned by the IO expander and the touch driver.
// ------------------------------------------------------------
static i2c_master_dev_handle_t devRTC  = NULL;   // DS3231  0x68
static i2c_master_dev_handle_t devSHT  = NULL;   // SHT3x   0x44
static i2c_master_dev_handle_t devLUX  = NULL;   // BH1750  0x23

// ------------------------------------------------------------
// DS3231
// ------------------------------------------------------------
#define RTC_ADDR      0x68
#define RTC_REG_TIME  0x00
#define RTC_REG_STAT  0x0F   // bit 7 = oscillator stop flag
#define RTC_REG_TEMP  0x11

struct Clock {
  uint8_t  sec, min, hour, dow, day, month;
  uint16_t year;
  bool     valid;      // read succeeded
  bool     wasStopped; // oscillator stop flag was set
};
static Clock now = { 0, 0, 0, 1, 1, 1, 2000, false, true };
static float rtcTempC = 0.0f;
static bool  rtcTempOK = false;

static uint8_t bcd2dec(uint8_t v) { return (uint8_t)((v >> 4) * 10 + (v & 0x0F)); }
static uint8_t dec2bcd(uint8_t v) { return (uint8_t)(((v / 10) << 4) | (v % 10)); }

static bool rtcReadRegs(uint8_t reg, uint8_t *buf, size_t len) {
  if (!devRTC) return false;
  return i2c_master_transmit_receive(devRTC, &reg, 1, buf, len, 100) == ESP_OK;
}

static bool rtcWriteRegs(uint8_t reg, const uint8_t *data, size_t len) {
  if (!devRTC || len > 16) return false;
  uint8_t tx[17];
  tx[0] = reg;
  memcpy(tx + 1, data, len);
  return i2c_master_transmit(devRTC, tx, len + 1, 100) == ESP_OK;
}

static void rtcDiagnosticDump(const char *reason) {
#if PANEL_ID == 2
  (void)reason;
  return;
#else
  uint8_t raw[7] = {0};
  uint8_t st = 0xFF;
  bool timeOK = rtcReadRegs(RTC_REG_TIME, raw, 7);
  bool statOK = rtcReadRegs(RTC_REG_STAT, &st, 1);

  Serial.println();
  Serial.printf("=== RTC DIAGNOSTIC: %s ===\n", reason ? reason : "manual");
  Serial.printf("RTC time read : %s\n", timeOK ? "OK" : "FAILED");

  if (timeOK) {
    uint8_t sec = bcd2dec(raw[0] & 0x7F);
    uint8_t min = bcd2dec(raw[1] & 0x7F);
    uint8_t hour = bcd2dec(raw[2] & 0x3F);
    uint8_t day = bcd2dec(raw[4] & 0x3F);
    uint8_t mon = bcd2dec(raw[5] & 0x1F);
    uint16_t yr = (uint16_t)(2000 + bcd2dec(raw[6]));

    Serial.printf("raw 00..06   : %02X %02X %02X %02X %02X %02X %02X\n",
                  raw[0], raw[1], raw[2], raw[3], raw[4], raw[5], raw[6]);
    Serial.printf("decoded       : %04u-%02u-%02u %02u:%02u:%02u\n",
                  yr, mon, day, hour, min, sec);
  }

  if (statOK)
    Serial.printf("RTC status    : OK  0x%02X  OSF=%u\n", st, (st & 0x80) ? 1 : 0);
  else
    Serial.println("RTC status    : FAILED");

  Serial.println("================================");
  Serial.println();
#endif
}
static uint8_t dayOfWeek(uint16_t y, uint8_t m, uint8_t d);

static uint16_t rsTxSeq = 0;
static uint32_t rsTxGoodAck = 0;
static uint32_t rsTxTimeout = 0;
static uint32_t rsTxBadAck = 0;

static bool rs485WaitForTimeAck(uint16_t wantedSeq) {
#if PANEL_ID == 1
  const uint32_t startMs = millis();
  TimeFrame rx{};

  while (millis() - startMs < 400) {
    if (!rsReadFrame(rx)) {
      delay(1);
      continue;
    }

    if (rx.crc != rsFrameCrc(rx)) {
      ++rsTxBadAck;
      continue;
    }

    const uint16_t seq = rsFrameSeq(rx);
    if (rx.src == NODE_IRA &&
        rx.dst == NODE_SHEMI &&
        rx.type == TYPE_ACK &&
        seq == wantedSeq) {
      ++rsTxGoodAck;
      Serial.printf("[485] RX IRA TIME ACK seq=%u RTT=%lu ms good=%lu timeout=%lu bad=%lu\n",
                    wantedSeq,
                    (unsigned long)(millis() - startMs),
                    (unsigned long)rsTxGoodAck,
                    (unsigned long)rsTxTimeout,
                    (unsigned long)rsTxBadAck);
      return true;
    }
    ++rsTxBadAck;
  }

  ++rsTxTimeout;
  Serial.printf("[485] TIMEOUT waiting IRA TIME ACK seq=%u timeout=%lu bad=%lu\n",
                wantedSeq,
                (unsigned long)rsTxTimeout,
                (unsigned long)rsTxBadAck);
#endif
  return false;
}

static void rs485ClockSendTick() {
#if PANEL_ID == 1
  static uint32_t lastSendMs = 0;
  const uint32_t ms = millis();
  if (ms - lastSendMs < 1000) return;
  lastSendMs = ms;

  if (!now.valid || now.wasStopped) {
    Serial.println("[RTC] CLOCK NOT READY - nothing sent");

    // TEST070: keep the evidence visible after Serial Monitor attaches.
    static uint32_t lastRtcDiagMs = 0;
    uint32_t diagNowMs = millis();
    if (lastRtcDiagMs == 0 || diagNowMs - lastRtcDiagMs >= 5000UL) {
      lastRtcDiagMs = diagNowMs;
      rtcDiagnosticDump("CLOCK NOT READY - live diagnostic");
    }
    return;
  }

  TimeFrame tx{};
  tx.start  = FRAME_START;
  tx.src    = NODE_SHEMI;
  tx.dst    = NODE_IRA;
  tx.type   = TYPE_TIME;
  tx.seqLo  = uint8_t(rsTxSeq & 0xFF);
  tx.seqHi  = uint8_t((rsTxSeq >> 8) & 0xFF);
  tx.yearLo = uint8_t(now.year & 0xFF);
  tx.yearHi = uint8_t((now.year >> 8) & 0xFF);
  tx.month  = now.month;
  tx.day    = now.day;
  tx.hour   = now.hour;
  tx.minute = now.min;
  tx.second = now.sec;
  tx.crc    = rsFrameCrc(tx);

  rsSendFrame(tx);
  Serial.printf("[RTC] %04u-%02u-%02u %02u:%02u:%02u -> [485] TX TIME seq=%u\n",
                now.year, now.month, now.day,
                now.hour, now.min, now.sec, rsTxSeq);

  rs485WaitForTimeAck(rsTxSeq);
  ++rsTxSeq;
#endif
}
static void rs485FeedbackPoll() {
#if PANEL_ID == 1
  TimeFrame ignored{};
  // rsReadFrame() also handles every 4-byte BedBox feedback frame it sees.
  // Any complete A5 frame left over here is simply drained; the synchronous
  // TIME send already waited for its matching ACK before we get here.
  while (rsReadFrame(ignored)) {
    // No action required for late/stale A5 frames on Shemi.
  }
#endif
}
static void rs485ClockPoll() {
#if PANEL_ID == 2
  TimeFrame rx{};

  while (rsReadFrame(rx)) {
    if (rx.crc != rsFrameCrc(rx)) {
      ++rsBadFrames;
      Serial.printf("[485] BAD CRC bad=%lu\n", (unsigned long)rsBadFrames);
      continue;
    }

    if (rx.dst != NODE_IRA && rx.dst != 0) continue;
    if (rx.src != NODE_SHEMI || rx.type != TYPE_TIME) continue;

    const uint16_t seq = rsFrameSeq(rx);

    if (!rsTimeFieldsValid(rx)) {
      ++rsBadFrames;
      Serial.printf("[485] INVALID TIME seq=%u bad=%lu\n",
                    seq, (unsigned long)rsBadFrames);
      continue;
    }

    now.year  = rsFrameYear(rx);
    now.month = rx.month;
    now.day   = rx.day;
    now.hour  = rx.hour;
    now.min   = rx.minute;
    now.sec   = rx.second;
    now.dow   = dayOfWeek(now.year, now.month, now.day);
    now.valid = true;
    now.wasStopped = false;

    ++rsGoodTimes;
    Serial.printf("[TIME] %04u-%02u-%02u %02u:%02u:%02u RX seq=%u good=%lu bad=%lu\n",
                  now.year, now.month, now.day,
                  now.hour, now.min, now.sec,
                  seq,
                  (unsigned long)rsGoodTimes,
                  (unsigned long)rsBadFrames);

    delay(2);
    TimeFrame ack = rsMakeAck(seq);
    rsSendFrame(ack);
    ++rsReplies;
    Serial.printf("[485] TX IRA TIME ACK seq=%u replies=%lu\n",
                  seq, (unsigned long)rsReplies);
  }
#endif
}

static void rtcRead() {
  static bool rtcBootDumpDone = false;
  if (!rtcBootDumpDone) {
    rtcBootDumpDone = true;
    rtcDiagnosticDump("first rtcRead after boot");
  }
#if PANEL_ID == 2
  return;  // Ira clock comes from Shemi over RS485.
#endif
  uint8_t b[7];
  if (!rtcReadRegs(RTC_REG_TIME, b, 7)) { now.valid = false; return; }

  now.sec   = bcd2dec(b[0] & 0x7F);
  now.min   = bcd2dec(b[1] & 0x7F);
  // Bit 6 set means 12-hour mode. The setter always writes 24-hour,
  // but a module fresh out of a bag can arrive in 12-hour mode, so
  // it is handled rather than assumed.
  if (b[2] & 0x40) {
    uint8_t h = bcd2dec(b[2] & 0x1F);
    if (b[2] & 0x20) { if (h != 12) h = (uint8_t)(h + 12); }
    else             { if (h == 12) h = 0; }
    now.hour = h;
  } else {
    now.hour = bcd2dec(b[2] & 0x3F);
  }
  // Register 0x03 is deliberately IGNORED. It only changes when
  // somebody sets the clock, so a wrong value written once stays
  // wrong forever - which is exactly what happened here. The day of
  // week follows from the date with no ambiguity, so compute it.
  // (The register is still written by rtcSet, for anything else
  // that reads this chip.)
  now.day   = bcd2dec(b[4] & 0x3F);
  now.month = bcd2dec(b[5] & 0x1F);
  now.year  = (uint16_t)(2000 + bcd2dec(b[6]));
  now.dow   = dayOfWeek(now.year, now.month, now.day);
  now.valid = true;

  uint8_t st;
  if (rtcReadRegs(RTC_REG_STAT, &st, 1)) now.wasStopped = (st & 0x80) != 0;

  uint8_t t[2];
  if (rtcReadRegs(RTC_REG_TEMP, t, 2)) {
    rtcTempC  = (float)(int8_t)t[0] + ((t[1] >> 6) * 0.25f);
    rtcTempOK = true;
  }
}

// Zeller. The RTC keeps a day-of-week counter but has no idea what
// a calendar is, so it must be handed the right number.
static uint8_t dayOfWeek(uint16_t y, uint8_t m, uint8_t d) {
  if (m < 3) { m = (uint8_t)(m + 12); y = (uint16_t)(y - 1); }
  uint16_t k = y % 100, j = y / 100;
  int h = (d + (13 * (m + 1)) / 5 + k + k / 4 + j / 4 + 5 * j) % 7;
  // h is 0 Saturday, 1 Sunday ... 6 Friday. The DS3231 counter here
  // is 1 Sunday .. 7 Saturday, which is +6 mod 7, not +5. The +5 in
  // TEST 011 through 016 shifted every day back by one.
  return (uint8_t)(((h + 6) % 7) + 1);
}

static const char *kDow[8] = { "", "Sun", "Mon", "Tue", "Wed", "Thu", "Fri", "Sat" };

static bool rtcSet(uint16_t y, uint8_t mo, uint8_t d,
                   uint8_t h, uint8_t mi, uint8_t se) {
  if (y < 2000 || y > 2099 || mo < 1 || mo > 12 || d < 1 || d > 31 ||
      h > 23 || mi > 59 || se > 59) return false;

  uint8_t b[7];
  b[0] = dec2bcd(se);
  b[1] = dec2bcd(mi);
  b[2] = dec2bcd(h);              // bit 6 clear = 24-hour
  b[3] = dayOfWeek(y, mo, d);
  b[4] = dec2bcd(d);
  b[5] = dec2bcd(mo);
  b[6] = dec2bcd((uint8_t)(y - 2000));
  if (!rtcWriteRegs(RTC_REG_TIME, b, 7)) return false;

  // Clear the oscillator stop flag. The time is now known good, so
  // the warning it carries has stopped being true.
  uint8_t st;
  if (rtcReadRegs(RTC_REG_STAT, &st, 1)) {
    st &= (uint8_t)~0x80;
    rtcWriteRegs(RTC_REG_STAT, &st, 1);
  }
  now.wasStopped = false;
  return true;
}

// ------------------------------------------------------------
// AT24C32 - the 4 KB EEPROM on the RTC module, address 0x57
//
// This is where every tuned value lives. It is not part of the
// ESP32, so reflashing the firmware does not touch it.
// ------------------------------------------------------------
#define EE_ADDR       0x57
#define EE_BASE       0x0000
#define EE_LEN        16        // one record, well inside one 32 byte page
#define EE_MAGIC0     0xB6
#define EE_MAGIC1     0x3D
#define EE_VERSION    1
#define EE_SETTLE_MS  3000UL    // quiet time before a write
#define EE_WRITE_MS   12        // ceiling on the write cycle poll

static i2c_master_dev_handle_t devEE = NULL;
static bool     cfgDirty      = false;
static uint32_t cfgTouchedAt  = 0;

static void cfgTouched() { cfgDirty = true; cfgTouchedAt = millis(); }

// After a page write the chip stops answering for about 5 ms while
// it burns. Poll until it acknowledges rather than guessing a delay
// that is either too short and corrupts, or too long and stalls.
static bool eeWaitReady() {
  // handle is a DEV_I2C_Port struct; the bus pointer is .bus inside
  // it. Same form probeAddr() has used since TEST 010.
  if (handle.bus == NULL) return false;
  uint32_t t0 = millis();
  while (millis() - t0 < EE_WRITE_MS) {
    if (i2c_master_probe(handle.bus, EE_ADDR, 5) == ESP_OK) return true;
    delay(1);
  }
  return false;
}

static uint8_t cfgSum(const uint8_t *b) {
  uint16_t sum = 0;
  for (int i = 0; i < EE_LEN - 1; i++) sum += b[i];
  return (uint8_t)(sum & 0xFF);
}

static bool cfgSave() {
  if (!devEE) return false;

  uint8_t b[EE_LEN];
  memset(b, 0, sizeof(b));
  b[0] = EE_MAGIC0;
  b[1] = EE_MAGIC1;
  b[2] = EE_VERSION;
  b[3] = (uint8_t)((autoBright ? 0x01 : 0) | (alarmOn   ? 0x02 : 0) |
                   (use12h     ? 0x04 : 0) | (alarmOnce ? 0x08 : 0));
  b[4] = blMin;
  b[5] = blMax;
  b[6] = autoSpeed;
  b[7] = hapDutyPct;
  b[8] = (uint8_t)(hapLenMs & 0xFF);
  b[9] = (uint8_t)(hapLenMs >> 8);
  b[10] = (uint8_t)(alarmMin & 0xFF);
  b[11] = (uint8_t)(alarmMin >> 8);
  // Byte 12: high nibble is the screensaver brightness in steps of
  // 4 percent. It was always zero before, and zero reads as "use
  // the default". The low nibble is the old five entry delay index,
  // kept only so an older record can still be translated.
  b[12] = (uint8_t)(((saverBright / 4) & 0x0F) << 4);
  b[13] = sleepMin;      // byte 13 was padding; 0 reads as the default
  // Byte 14: the new delay index PLUS ONE, so zero still means
  // "never written" and the fallback above can fire.
  b[14] = (uint8_t)(saverIdx + 1);
  b[EE_LEN - 1] = cfgSum(b);

  // Two address bytes, high then low. The AT24C02 on some other RTC
  // modules takes one; sending one byte here writes to the wrong
  // place and reads back nonsense.
  uint8_t tx[2 + EE_LEN];
  tx[0] = (uint8_t)(EE_BASE >> 8);
  tx[1] = (uint8_t)(EE_BASE & 0xFF);
  memcpy(tx + 2, b, EE_LEN);

  if (i2c_master_transmit(devEE, tx, sizeof(tx), 100) != ESP_OK) {
    Serial.println("[cfg] write failed");
    return false;
  }
  eeWaitReady();
  Serial.println("[cfg] saved");
  return true;
}

static void cfgLoad() {
  if (!devEE) { Serial.println("[cfg] no EEPROM - using defaults"); return; }

  uint8_t a[2] = { (uint8_t)(EE_BASE >> 8), (uint8_t)(EE_BASE & 0xFF) };
  uint8_t b[EE_LEN];
  if (i2c_master_transmit_receive(devEE, a, 2, b, EE_LEN, 100) != ESP_OK) {
    Serial.println("[cfg] read failed - using defaults");
    return;
  }

  // A blank EEPROM is all 0xFF and a changed layout makes old bytes
  // mean something else. Either loads as garbage, so all three
  // checks have to pass before a single value is believed.
  if (b[0] != EE_MAGIC0 || b[1] != EE_MAGIC1) {
    Serial.println("[cfg] empty - using defaults, will save on first change");
    return;
  }
  if (b[2] != EE_VERSION) {
    Serial.printf("[cfg] version %u, expected %u - using defaults\n",
                  b[2], EE_VERSION);
    return;
  }
  if (b[EE_LEN - 1] != cfgSum(b)) {
    Serial.println("[cfg] checksum bad - using defaults");
    return;
  }

  autoBright = (b[3] & 0x01) != 0;
  alarmOn    = (b[3] & 0x02) != 0;
  // Bit 2 was always zero before TEST 028, so an older record reads
  // as 24 hour - which is what it was. No version bump needed.
  use12h     = true;   // TEST073: display is always 12-hour AM/PM
  alarmOnce  = (b[3] & 0x08) != 0;   // 0 = every day, as older records meant
  blMin      = b[4];
  blMax      = b[5];
  autoSpeed  = b[6];
  hapDutyPct = b[7];
  hapLenMs   = (uint16_t)(b[8] | (b[9] << 8));
  alarmMin   = (int)(b[10] | (b[11] << 8));
  if (b[14] >= 1 && b[14] <= 9) {
    saverIdx = (uint8_t)(b[14] - 1);
  } else {
    // Written before TEST 039. Translate the old five entry index
    // rather than throw the setting away.
    uint8_t old = b[12] & 0x0F;
    saverIdx = (old <= 4) ? kSaverLegacy[old] : 5;
  }
  saverAfterMs = kSaverOpts[saverIdx];

  { uint8_t sb = (uint8_t)(((b[12] >> 4) & 0x0F) * 4);
    saverBright = (sb >= 1 && sb <= 60) ? sb : 8; }

  sleepMin     = (b[13] >= 1 && b[13] <= 60) ? b[13] : 30;

  // Range checks even after the checksum passes. A good checksum
  // only proves the bytes are the ones that were written, not that
  // they were sensible when they were.
  if (blMin < 1   || blMin > 100)  blMin = 12;
  if (blMax < 1   || blMax > 100)  blMax = 100;
  if (blMax < blMin)               blMax = blMin;
  if (autoSpeed < AUTO_SPEED_MIN || autoSpeed > AUTO_SPEED_MAX) autoSpeed = 6;
  if (hapDutyPct > 100)            hapDutyPct = 100;
  if (hapLenMs < 20 || hapLenMs > 500) hapLenMs = 150;
  if (alarmMin < 0 || alarmMin > 1439) alarmMin = 7 * 60;

  Serial.printf("[cfg] loaded: auto %d  %u-%u%%  speed %u  "
                "haptic %u%%/%ums  alarm %02d:%02d %s\n",
                autoBright, blMin, blMax, autoSpeed, hapDutyPct, hapLenMs,
                alarmMin / 60, alarmMin % 60, alarmOn ? "on" : "off");
}

// Called once a second from sensorTick, which already runs in the
// LVGL task - the same task that owns the bus.
static void cfgTick() {
  if (!cfgDirty) return;
  if (millis() - cfgTouchedAt < EE_SETTLE_MS) return;
  cfgDirty = false;
  cfgSave();
}

// ------------------------------------------------------------
// SHT3x
//
// Periodic mode, and the result is fetched in ONE transaction:
// the fetch command and the six data bytes are joined by a
// repeated START, so no other transfer on the bus can land in the
// middle of it. TEST 012 split the command and the read across two
// separate ticks, and something in the gap was discarding the
// pending measurement.
//
// 0.5 measurements per second, high repeatability. Slow on purpose
// - the sensor warms itself while measuring, and a bedroom does not
// change temperature in one second.
// ------------------------------------------------------------
#define SHT_ADDR      0x44
#define SHT_CMD_BREAK 0x3093   // leave any periodic mode
#define SHT_CMD_RESET 0x30A2   // soft reset - defined, not used
#define SHT_CMD_PER   0x2032   // periodic, 0.5 mps, high repeatability
#define SHT_CMD_FETCH 0xE000   // fetch the last result

// SHT_STALE_MS must be comfortably longer than the measurement
// interval, or normal gaps look like faults. At 0.5 mps a new value
// arrives every 2 s, so 15 s is roughly seven missed measurements -
// long past coincidence.
#define SHT_STALE_MS 15000

static float shtTempC = 0.0f, shtRH = 0.0f;
static bool     shtOK = false;          // have a value worth showing
static uint32_t shtLastGood = 0;        // millis() of the last good fetch
static const char *shtMsg = "not started";

// CRC-8, polynomial 0x31, init 0xFF. Sensirion checksums every
// value; an unchecked reading off a cable is a guess.
static uint8_t shtCRC(const uint8_t *d, int len) {
  uint8_t c = 0xFF;
  for (int i = 0; i < len; i++) {
    c ^= d[i];
    for (int b = 0; b < 8; b++)
      c = (c & 0x80) ? (uint8_t)((c << 1) ^ 0x31) : (uint8_t)(c << 1);
  }
  return c;
}

static bool shtCmd(uint16_t cmd) {
  if (!devSHT) return false;
  uint8_t b[2] = { (uint8_t)(cmd >> 8), (uint8_t)(cmd & 0xFF) };
  return i2c_master_transmit(devSHT, b, 2, 100) == ESP_OK;
}

// Called at boot and again after repeated failures. Break first:
// a sensor already in periodic mode from a previous run rejects a
// new mode command until it is stopped.
static void shtBegin() {
  if (!devSHT) { shtMsg = "no handle"; return; }
  shtLastGood = millis();
  shtCmd(SHT_CMD_BREAK);
  delay(2);
  bool ok = shtCmd(SHT_CMD_PER);
  shtMsg = ok ? "armed" : "arm failed";
}

static void shtRead() {
  if (!devSHT) { shtOK = false; shtMsg = "no handle"; return; }

  uint8_t cmd[2] = { (uint8_t)(SHT_CMD_FETCH >> 8),
                     (uint8_t)(SHT_CMD_FETCH & 0xFF) };
  uint8_t b[6];

  // One transaction. Repeated START between the command and the
  // read, so nothing can get in between.
  if (i2c_master_transmit_receive(devSHT, cmd, 2, b, 6, 100) != ESP_OK) {
    // NOT A FAILURE. In periodic mode a fetch with no new
    // measurement ready is deliberately not acknowledged. Keep the
    // last value and say nothing.
    if (shtOK && (millis() - shtLastGood) > SHT_STALE_MS) {
      shtOK  = false;
      shtMsg = "stale - rearming";
      shtBegin();
    } else if (!shtOK && (millis() - shtLastGood) > SHT_STALE_MS) {
      shtMsg = "no data - rearming";
      shtLastGood = millis();     // do not rearm again for another window
      shtBegin();
    }
    return;
  }

  if (shtCRC(b, 2) != b[2] || shtCRC(b + 3, 2) != b[5]) {
    // This one IS a fault. The sensor answered and the bytes are
    // corrupt, which is electrical: cable length, pull-ups, noise.
    shtMsg = "CRC bad";
    return;
  }

  uint16_t rawT = (uint16_t)((b[0] << 8) | b[1]);
  uint16_t rawH = (uint16_t)((b[3] << 8) | b[4]);
  shtTempC = -45.0f + 175.0f * ((float)rawT / 65535.0f);
  shtRH    = 100.0f * ((float)rawH / 65535.0f);
  shtOK       = true;
  shtMsg      = "ok";
  shtLastGood = millis();
}

// ------------------------------------------------------------
// BH1750 - not answering yet, driver ready for when it is
// ------------------------------------------------------------
#define LUX_ADDR 0x23

static float luxVal = 0.0f;
static bool  luxOK = false;
static bool  luxStarted = false;

static void luxBegin() {
  if (!devLUX) return;
  const uint8_t cmd = 0x10;   // continuous, high resolution, ~120 ms
  luxStarted = (i2c_master_transmit(devLUX, &cmd, 1, 100) == ESP_OK);
}

static void luxRead() {
  if (!devLUX) { luxOK = false; return; }
  if (!luxStarted) { luxBegin(); if (!luxStarted) { luxOK = false; return; } }
  uint8_t b[2];
  if (i2c_master_receive(devLUX, b, 2, 100) != ESP_OK) {
    luxOK = false; luxStarted = false; return;   // retry the mode command later
  }
  luxVal = (float)((b[0] << 8) | b[1]) / 1.2f;
  luxOK  = true;
}

static lv_obj_t *tileBedImg   = NULL;
static lv_obj_t *tileRadioImg = NULL;
static lv_obj_t *tileACImg    = NULL;
static lv_obj_t *tileShadeImg = NULL;
static lv_obj_t *tileLampImg  = NULL;
static lv_obj_t *tileFanImg   = NULL;

// Each photographic tile is tracked as a button plus its image plus
// a pointer to the flag that says whether it is lit, so one function
// can repaint all of them.
struct Tile {
  lv_obj_t *btn;
  lv_obj_t *img;
  bool     *state;
};
static Tile  tiles[8];
static int   tileCount = 0;

// Panel-side state. Nothing reports back yet, so this is the only
// truth the screen has - exactly as on the old panel.
static bool bedRunning  = false;
static bool radioOn     = false;
static bool acPower     = false;
static int  acTemp      = 24;
static bool shadeOpen   = true;
static bool lampOn      = false;
static bool fanOn       = false;
static int  fanSpeed    = 0;
// What the short press returns to. 2 is the middle speed, used only
// if the fan has never been set this session.
static int  lastFanSpeed = 0;

// ------------------------------------------------------------
// Defined below setup(), declared here so setup() can call them.
static void applyBacklight(uint8_t v);
static void applyBacklightQuiet(uint8_t v);
static void printHelp();
static void refreshHomeTiles();
static void refreshAC();
static void refreshFan();
static void buildSettings();
static void buildMassage();
static void buildRadio();
static void buildAC();
static void buildFan();
static void buildAlarm();
static void lvMem(const char *what);
static void autoBrightTick();
static void saverTick();
static void sleepTick();
static void massTick();
static void saverEnter();
static void fastTick(lv_timer_t *t);
static void cfgTouched();
static void cfgTick();
static void alarmTick();
static void refreshAlarm();
static void sensorTick(lv_timer_t *t);

static void say(const char *what) {
  Serial.printf("[tile] %s\n", what);
  if (lblStatus) lv_label_set_text(lblStatus, what);
}

// paintTile() is defined further down, next to the other drawing
// helpers, so it is declared here for the event handlers above it.
static void paintTile(const struct Tile &t);

// Find the tile that owns an image object, so a handler can repaint
// just its own tile without a second lookup table.
static void repaintOwner(lv_obj_t *img) {
  for (int i = 0; i < tileCount; i++)
    if (tiles[i].img == img) { paintTile(tiles[i]); return; }
}

static void evBed(lv_event_t *e) {
  if (!scrMassage) { buildMassage(); lvMem("massage"); }          // built the first time it is opened
  if (scrMassage) lv_scr_load(scrMassage); else say("massage screen failed to build");
}

static void evRadio(lv_event_t *e) {
  if (!scrRadio) { buildRadio(); lvMem("radio"); }          // built the first time it is opened
  if (scrRadio) lv_scr_load(scrRadio); else say("radio screen failed to build");
}

// Fan and AC tiles: a short press flips the power and stays here, a
// 2 second hold opens the detail screen.
//
// THE HOLD IS TIMED HERE. LV_EVENT_LONG_PRESSED depends on the
// input driver's long_press_time, which lives inside Waveshare's
// port; TEST 046 set it blind at boot and the long press never
// fired. millis() on press and on release is exact and depends on
// nothing.
#define TILE_HOLD_MS 2000

static uint32_t tilePressMs = 0;

static void evTilePress(lv_event_t *e) { tilePressMs = millis(); }

// True if this was a hold. Also prints the measured time, so a
// threshold that turns out wrong can be changed against real
// numbers instead of guesses.
static bool tileWasHeld(const char *what) {
  uint32_t held = millis() - tilePressMs;
  Serial.printf("[tile] %s held %lu ms\n", what, (unsigned long)held);
  Serial.flush();
  return (tilePressMs != 0) && (held >= TILE_HOLD_MS);
}

static void evACRelease(lv_event_t *e) {
  bool hold = tileWasHeld("AC");
  tilePressMs = 0;
  if (hold) {
    if (!scrAC) { buildAC(); lvMem("AC"); }
    if (scrAC) lv_scr_load(scrAC); else say("AC screen failed to build");
    return;
  }
  acPower = !acPower;
  refreshAC();
  refreshHomeTiles();
  say(acPower ? "AC on" : "AC off");
}

// Slide off the tile and nothing happens - the standard way out of
// a press you did not mean.
static void evTileLost(lv_event_t *e) { tilePressMs = 0; }

static void evShade(lv_event_t *e) {
  shadeOpen = !shadeOpen;
  lv_img_set_src(tileShadeImg, shadeOpen ? &img_shade_open : &img_shade_closed);
  repaintOwner(tileShadeImg);
  say(shadeOpen ? "shutters open" : "shutters closed");
}

static void evLamp(lv_event_t *e) {
  lampOn = !lampOn;
  // The lamp has one photograph and two colours, applied once on
  // press. Nothing repaints on a timer - that was the old jitter.
  // The lamp is tinted rather than blackened - amber when lit, cold
  // grey when not - so it needs its own recolour, then the shared
  // opacity and background rule on top.
  lv_obj_set_style_img_recolor(tileLampImg,
      lv_color_hex(lampOn ? 0xE8A030 : 0x9098A0), 0);
  repaintOwner(tileLampImg);
  say(lampOn ? "lamp on" : "lamp off");
}

static void evFanRelease(lv_event_t *e) {
  bool hold = tileWasHeld("fan");
  tilePressMs = 0;
  if (hold) {
    if (!scrFan) { buildFan(); lvMem("fan"); }
    if (scrFan) lv_scr_load(scrFan); else say("fan screen failed to build");
    return;
  }
  if (fanSpeed > 0) { lastFanSpeed = fanSpeed; fanSpeed = 0; }
  else              { fanSpeed = (lastFanSpeed > 0) ? lastFanSpeed : 2; }
  fanOn = (fanSpeed > 0);
  refreshFan();
  refreshHomeTiles();
  say(fanOn ? "fan on" : "fan off");
}

// evFanLong went with the LVGL long-press approach; evFanRelease
// above does the same job from its own timing.

static void evSettings(lv_event_t *e) {
  if (!scrSettings) { buildSettings(); lvMem("settings"); }
  if (scrSettings) lv_scr_load(scrSettings);
  else             say("settings screen failed to build");
}
static void evSpare(lv_event_t *e) {
  if (!scrAlarm) { buildAlarm(); lvMem("alarm"); }
  if (scrAlarm) lv_scr_load(scrAlarm); else say("alarm screen failed to build");
}

// ------------------------------------------------------------

static int tileX(int c) { return TILE_X0 + c * (TILE_SZ + TILE_GAPX); }
static int tileY(int r) { return TILE_Y0 + r * (TILE_SZ + TILE_GAPY); }

// ------------------------------------------------------------
// TOUCH FEEDBACK
//
// Coin ERM motor module on GPIO 6. IN to GPIO 6, VCC to the same
// 5 V that feeds the board, GND common.
//
// Numbers that came from a meter, not from a listing:
//   22 mA at 3.3 V spinning
//   36 mA at 5 V spinning
//   under 1 mA into IN, so the gate is a MOSFET
//   535 mV across the motor pads in diode mode - flyback present
// ------------------------------------------------------------
#define HAPTIC_PIN       6
#define HAPTIC_FREQ      20000   // above hearing - this sits on a headboard
#define HAPTIC_BITS      8
// The two tunables live further up, beside the brightness ones,
// because the EEPROM code above needs to see all of them.

static lv_timer_t *hapTimer = NULL;
static bool        hapReady = false;

static inline uint32_t hapDuty() {
  return ((1u << HAPTIC_BITS) - 1) * hapDutyPct / 100;
}

// Ends the tick. The timer parks itself - nothing runs between
// touches.
static void hapTick(lv_timer_t *t) {
  ledcWrite(HAPTIC_PIN, 0);
  lv_timer_pause(t);
}

// Retriggering during a pulse restarts it rather than stacking
// timers, so a fast series of taps cannot leave the motor latched
// on.
static void hapticFire(uint8_t pct, uint16_t ms) {
  if (!hapReady || !hapTimer) return;
  if (pct > 100) pct = 100;
  ledcWrite(HAPTIC_PIN, ((1u << HAPTIC_BITS) - 1) * pct / 100);
  lv_timer_set_period(hapTimer, ms);
  lv_timer_reset(hapTimer);
  lv_timer_resume(hapTimer);
}

static void hapticPulse() { hapticFire(hapDutyPct, hapLenMs); }

static void hapticInit() {
  hapReady = ledcAttach(HAPTIC_PIN, HAPTIC_FREQ, HAPTIC_BITS);
  if (hapReady) ledcWrite(HAPTIC_PIN, 0);
  hapTimer = lv_timer_create(hapTick, hapLenMs, NULL);
  lv_timer_pause(hapTimer);
  Serial.printf("haptic: GPIO %d  %s  %u%% duty  %u ms\n",
                HAPTIC_PIN, hapReady ? "attached" : "ATTACH FAILED",
                hapDutyPct, hapLenMs);
}

// One handler for the entire screen. Tiles bubble their events up
// to it; bare background reaches it directly. Any tile added later
// is covered with no change here.
static void evAnyPress(lv_event_t *e) {
  (void)e;
  lastTouchMs = millis();       // any touch anywhere postpones the screensaver
  hapticPulse();
}

// ------------------------------------------------------------

static lv_obj_t *makeTile(int col, int row, uint32_t bg) {
  lv_obj_t *b = lv_btn_create(scrHome);
  lv_obj_set_size(b, TILE_SZ, TILE_SZ);
  lv_obj_set_pos(b, tileX(col), tileY(row));
  lv_obj_set_style_bg_color(b, lv_color_hex(bg), 0);
  lv_obj_set_style_radius(b, 16, 0);
  lv_obj_set_style_pad_all(b, 0, 0);
  lv_obj_set_style_shadow_width(b, 0, 0);
  lv_obj_clear_flag(b, LV_OBJ_FLAG_SCROLLABLE);
  lv_obj_add_flag(b, LV_OBJ_FLAG_EVENT_BUBBLE);   // press reaches scrHome
  return b;
}

static lv_obj_t *addImg(lv_obj_t *parent, const lv_img_dsc_t *src) {
  lv_obj_t *im = lv_img_create(parent);
  lv_img_set_src(im, src);
  lv_obj_center(im);
  lv_obj_set_style_img_recolor(im, lv_color_black(), 0);
  lv_obj_set_style_img_recolor_opa(im, dimOff, 0);
  return im;
}

// Paint one tile according to its own state. Both the artwork and
// the panel behind it move together.
static void paintTile(const struct Tile &t) {
  bool on = t.state ? *t.state : false;
  lv_obj_set_style_img_recolor_opa(t.img, on ? dimOn : dimOff, 0);
  lv_obj_set_style_bg_color(t.btn,
      lv_color_hex(on ? TILE_BG_ON : TILE_BG_OFF), 0);
}
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
