shemtov/Bg_Bed/panel_ira/include/fan_img.h

#pragma once
// ==========================================================
//  fan_img.h - the ceiling fan tile, 200x200 RGB565
//
//  Made from the photograph of the actual fan in the room.
//  White blades on a white background, so they were cut out
//  by luminance rather than colour, then redrawn in soft
//  off-white on a dark slate-violet ground.
//
//    bed #4A3E2E amber   radio #2E4238 green
//    ac  #2C3C4A blue    fan   #221E2C violet, darkened
//
//  Byte order is LITTLE endian, low byte first, exactly as
//  tile_img.h stores its tiles. Get that backwards and the
//  colours come out wrong while the picture stays perfectly
//  recognisable - the hardest kind of mistake to spot.
// ==========================================================
#include <Arduino.h>
#include <lvgl.h>

const uint8_t img_fan_map[] = {
  0xE5, 0x20, 0xE5, 0x20, 0xE5, 0x20, 0xE5, 0x20, 0xE5, 0x20, 0xE5, 0x20, 0xE5, 0x20, 0xE5, 0x20,
  0xE5, 0x20, 0xE5, 0x20, 0xE5, 0x20, 0xE5, 0x20, 0xE5, 0x20, 0xE5, 0x20, 0xE5, 0x20, 0xE5, 0x20,
  0xE5, 0x20, 0xE5, 0x20, 0xE5, 0x20, 0xE5, 0x20, 0xE5, 0x20, 0xE5, 0x20, 0xE5, 0x20, 0xE5, 0x20,
  0xE5, 0x20, 0xE5, 0x20, 0xE5, 0x20, 0xE5, 0x20, 0xE5, 0x20, 0xE5, 0x20, 0xE5, 0x20, 0xE5, 0x20,
  0xE5, 0x20, 0xE5, 0x20, 0xE5, 0x20, 0xE5, 0x20, 0xE5, 0x20, 0xE5, 0x20, 0xE5, 0x20, 0xE5, 0x20,
  0xE5, 0x20, 0xE5, 0x20, 0xE5, 0x20, 0xE5, 0x20, 0xE5, 0x20, 0xE5, 0x20, 0xE5, 0x20, 0xE5, 0x20,
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
  0xE5, 0x20, 0xE5, 0x20, 0xE5, 0x20, 0xE5, 0x20, 0xE5, 0x20, 0xE5, 0x20, 0xE5, 0x20, 0xE5, 0x20,
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
};

const lv_img_dsc_t img_fan = {
  .header = { .cf = LV_IMG_CF_TRUE_COLOR, .always_zero = 0,
              .reserved = 0, .w = 200, .h = 200 },
  .data_size = 80000,
  .data = img_fan_map,
};
