shemtov/Bg_Bed/panel_ira/include/temp_font.h

#pragma once
// ============================================================
//  TEST 080 - temperature font, regenerated LARGER
//  Digits were 62 x 80. They are now about 104 px tall, one
//  clear step up, and the C grew with them so the block still
//  balances. The character range 0x2D..0x43 is unchanged, so
//  main.cpp needs no edit to use this file.
//  Generated from DejaVuSans-Bold.ttf
// ============================================================
#include <Arduino.h>
#include <gfxfont.h>

// ---- TempBig: rendered at 137 px, 13826 bytes of bitmap ----
const uint8_t TempBig_Bitmaps[] PROGMEM = {
  0x01, 0xFF, 0xFF, 0xFF, 0xFF, 0xFF, 0x80, 0x00, 0xFF, 0xFF, 0xFF, 0xFF, 0xFF, 0xC0, 0x00, 0x7F,
  0xFF, 0xFF, 0xFF, 0xFF, 0xE0, 0x00, 0x3F, 0xFF, 0xFF, 0xFF, 0xFF, 0xF0, 0x00, 0x1F, 0xFF, 0xFF,
  0xFF, 0xFF, 0xF8, 0x00, 0x0F, 0xFF, 0xFF, 0xFF, 0xFF, 0xFC, 0x00, 0x07, 0xFF, 0xFF, 0xFF, 0xFF,
  0xFE, 0x00, 0x03, 0xFF, 0xFF, 0xFF, 0xFF, 0xFF, 0x00, 0x01, 0xFF, 0xFF, 0xFF, 0xFF, 0xFF, 0x80,
  0x00, 0xFF, 0xFF, 0xFF, 0xFF, 0xFF, 0xC0, 0x00, 0x7F, 0xFF, 0xFF, 0xFF, 0xFF, 0xE0, 0x00, 0x3F,
  0xFF, 0xFF, 0xFF, 0xFF, 0xF0, 0x00, 0x1F, 0xFF, 0xFF, 0xFF, 0xFF, 0xF8, 0x00, 0x0F, 0xFF, 0xFF,
  0xFF, 0xFF, 0xFC, 0x00, 0x07, 0xFF, 0xFF, 0xFF, 0xFF, 0xFE, 0x00, 0x03, 0xFF, 0xFF, 0xFF, 0xFF,
  0xFF, 0x00, 0x01, 0xFF, 0xFF, 0xFF, 0xFF, 0xFF, 0x80, 0x00, 0xFF, 0xFF, 0xFF, 0xFF, 0xFF, 0xC0,
  0x00, 0x7F, 0xFF, 0xFF, 0xFF, 0xFF, 0xE0, 0x00, 0x00, 0x00, 0x00, 0x00, 0x00, 0x00, 0x00, 0x00,
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
  {   1342,    0,    0,   11,    0,     0 },   // 'A'
  {   1342,    0,    0,   11,    0,     0 },   // 'B'
  {   1342,   33,   34,   33,    0,     0 },   // 'C'
};

const GFXfont TempSmall PROGMEM = {
  (uint8_t *)TempSmall_Bitmaps,
  (GFXglyph *)TempSmall_Glyphs,
  0x2D, 0x43, 44
};
